hubertciebiada/open-ambient-sensor/hardware/photos/v0.54-mounted-led-ring.jpg

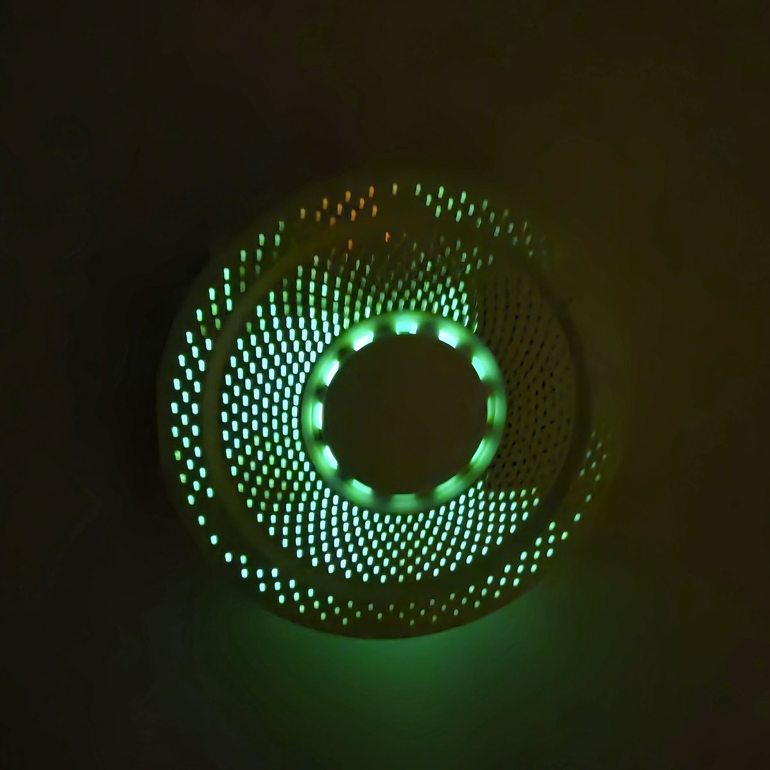
hardware/photos/v0.54-mounted-led-ring.jpg
