hubertciebiada/open-ambient-sensor/hardware/renders/pcb/2d-bottom.png

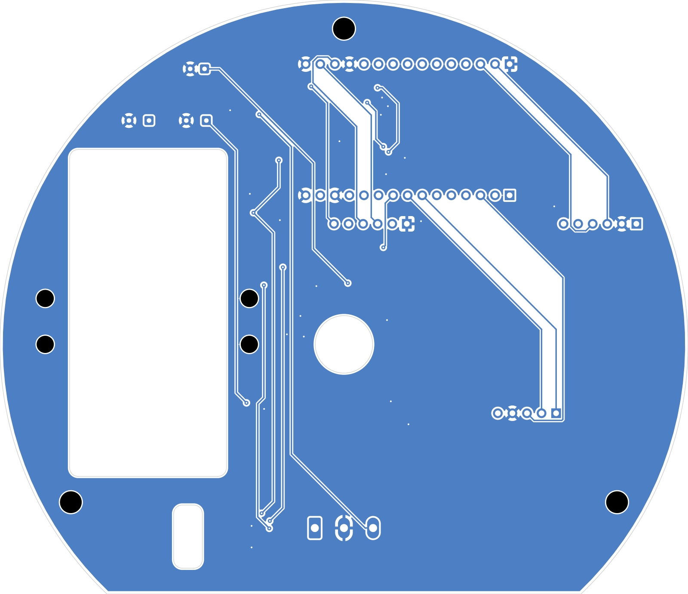
hardware/renders/pcb/2d-bottom.png
