hubertciebiada/open-ambient-sensor/hardware/renders/pcb/2d-cutouts.png

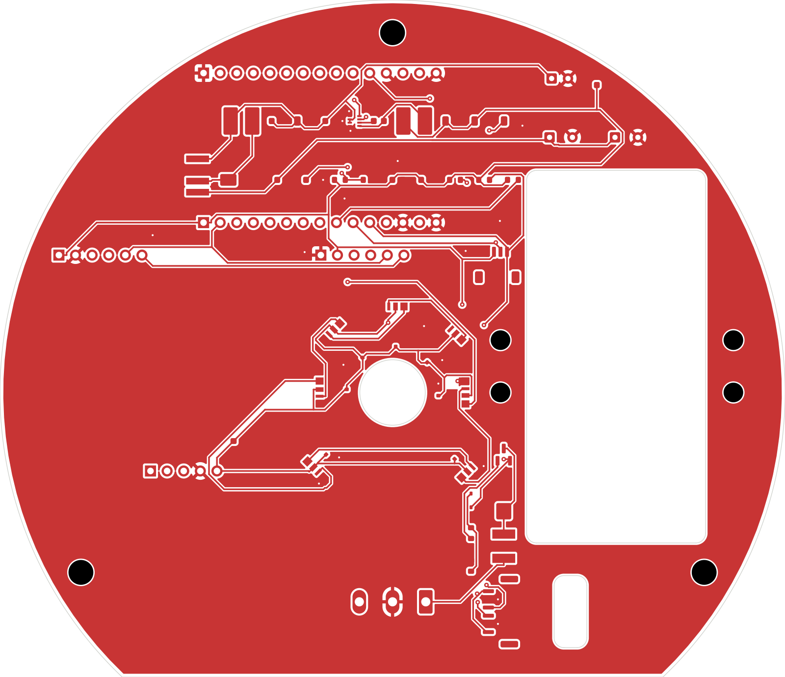
hardware/renders/pcb/2d-cutouts.png
