hubertciebiada/open-ambient-sensor/hardware/renders/pcb/3d-iso-90.png

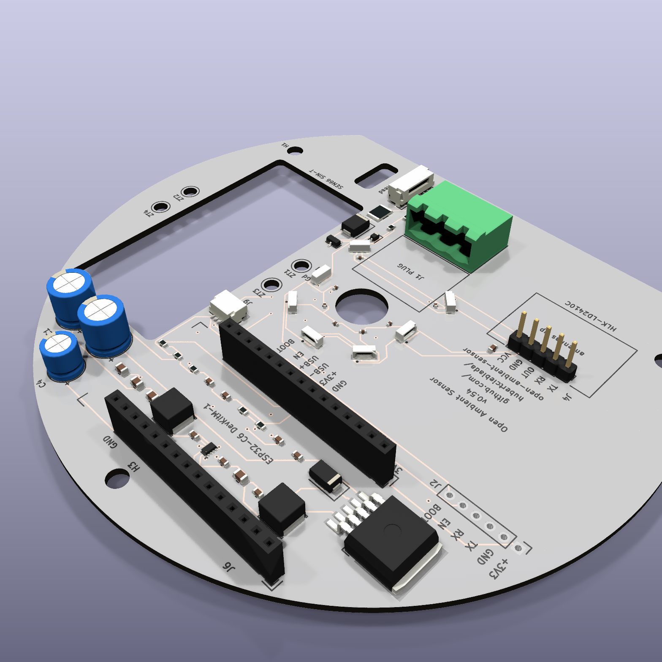
hardware/renders/pcb/3d-iso-90.png
