hubertciebiada/open-ambient-sensor/hardware/renders/pcb/3d-iso-270.png

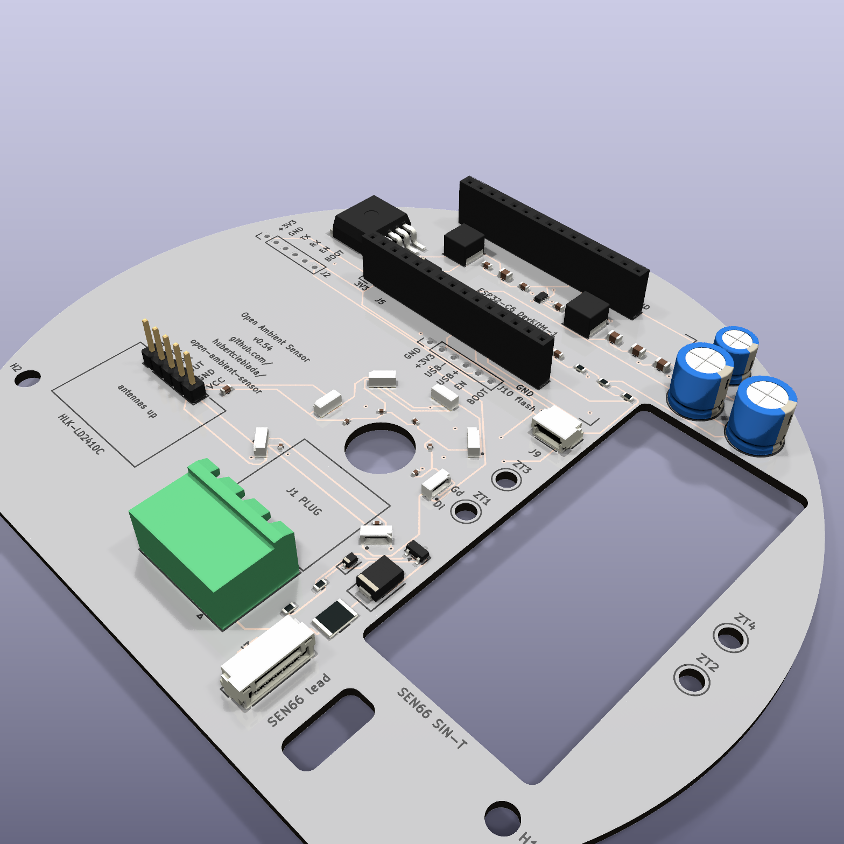
hardware/renders/pcb/3d-iso-270.png
