hubertciebiada/open-ambient-sensor/hardware/renders/sch/sch-io.png

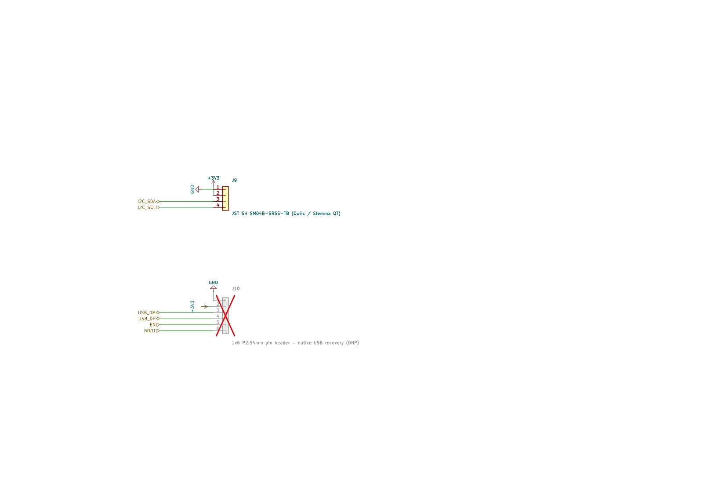
hardware/renders/sch/sch-io.png
