hubertciebiada/open-ambient-sensor/hardware/renders/sch/sch-mcu.png

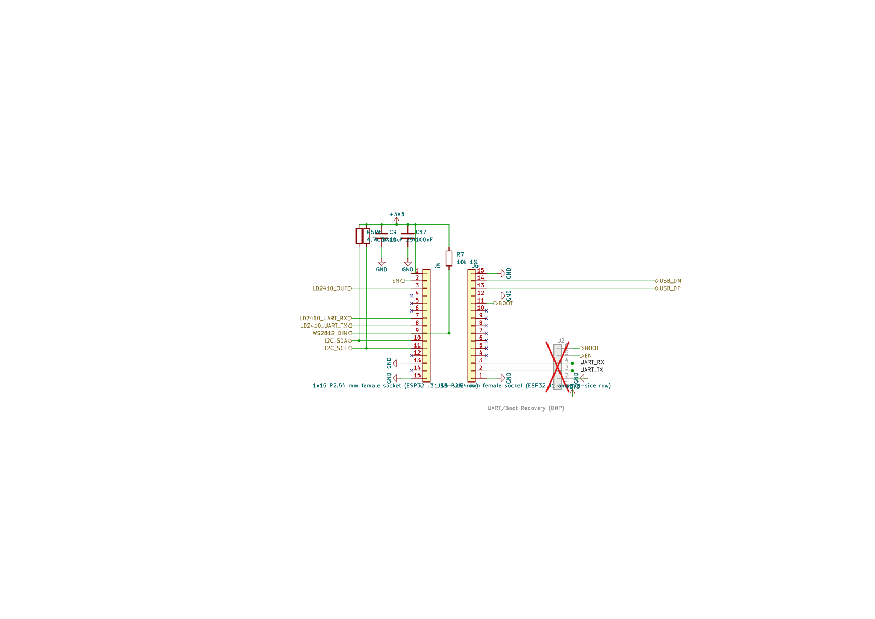
hardware/renders/sch/sch-mcu.png
