hubertciebiada/open-ambient-sensor/hardware/renders/sch/sch-power.png

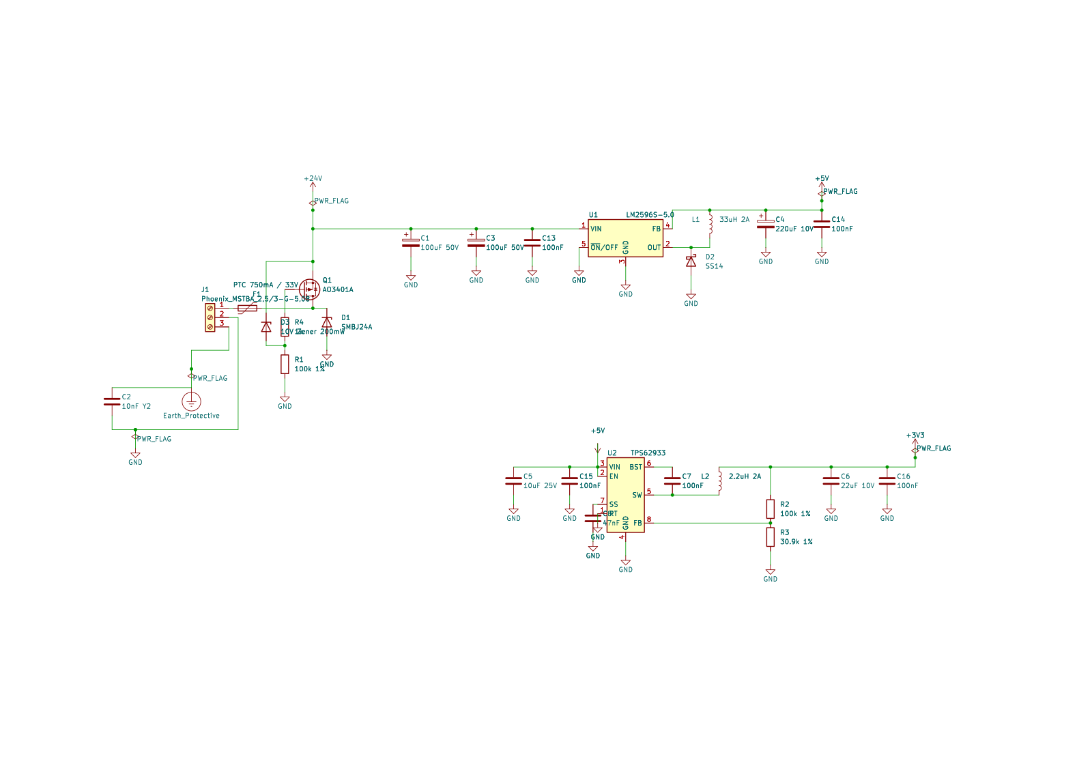
hardware/renders/sch/sch-power.png
