hubertciebiada/open-ambient-sensor/hardware/renders/sch/sch-sensors.png

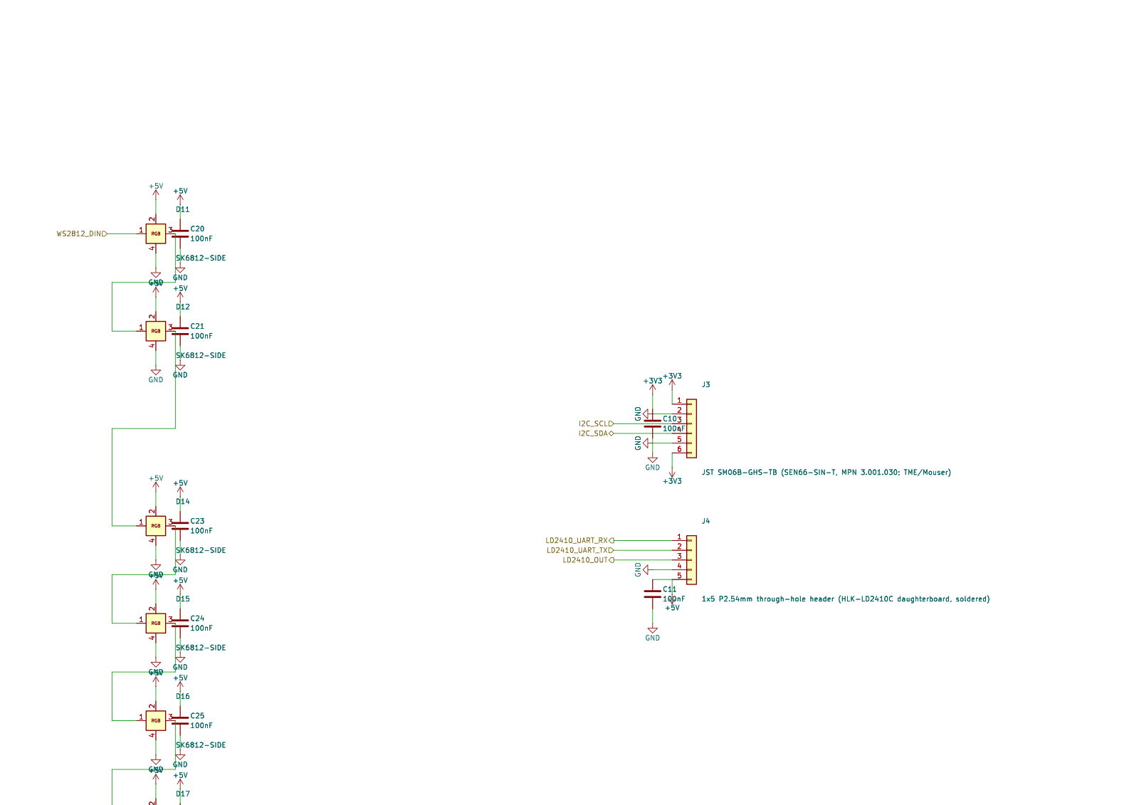
hardware/renders/sch/sch-sensors.png
