hubertciebiada/open-ambient-sensor/hardware/kicad/pipeline/oas/19_check_oas_metadata.py

"""Stage 19: metadata integrity checks on OAS source-of-truth dicts.

Five checks, one stage:

A. `boardgen._project.EXTERNAL_MODULES` (Lesson 10): every dev-module /
   dev-board / breakout entry MUST carry at least one canonical part
   identifier. We accept ANY of:
     - `mpn`                 (manufacturer part number)
     - `ean`                 (EAN/GTIN — Polish/EU retail preferred)
     - `material`            (Sensirion's canonical SKU)
     - `supplier_*` field    (specific distributor SKU or URL)
   Pure descriptive entries ('ESP32-C6 SuperMini' without MPN/EAN) are
   exactly the foot-gun this check prevents.

B. `lcsc_mapping.LCSC_MAPPING` self-consistency (Gap H + Lesson 5):
   - LCSC key matches pattern `^C\\d+$`,
   - `library` ∈ {Basic, Extended, N/A},
   - `manufacturer` and `mpn` both non-empty strings,
   - `datasheet` is a string (URL or empty placeholder).

   These guard against copy-paste typos like `C2302` vs `C23022` where
   one digit off lands on a completely different part (Lesson 5 R3
   near-miss: C23022 = 30.9 kΩ vs C23116 = 806 Ω).

C. `boardgen._project.POWER_BUDGET` schema (Lesson 6 — don't hallucinate
   datasheet values): every entry MUST carry
     - `name`, `rail`, `typ_ma`, `peak_ma`, `datasheet`,
   and the `datasheet` MUST be a non-empty HTTP/HTTPS URL. This forces
   anyone touching the power budget to cite a real datasheet — caught
   the same class of "I remember the AO3401A is ±20 V Vgs" error
   audit-16 caught (actually ±12 V) before it can land in the budget.

D. J4 (HLK-LD2410C) pin order vs Lesson 20 canonical mapping. Authority:
   Hi-Link HLK-LD2410C manual V1.00 (2022-11-07) Table 1 / section 4.2,
   read with the module ANTENNA-FACE UP and its pin row along the north
   edge (board-owner spec, 2026-07-21) — pin 1 = UART Tx, pin 2 = UART
   Rx, pin 3 = OUT, pin 4 = GND, pin 5 = VCC. Two anchors are verified:
     - `boardgen/_sch_sensors.py` J4 wiring block: each J4 pin's wire
       (uuid tags "j4-p1-tx" … "j4-p5-vcc-down") must terminate at the
       canonical net. Net-name nuance: the OAS net names are MCU-centric,
       so J4 pin 1 (the module's UART_Tx OUTPUT) lands on net
       LD2410_UART_RX (it arrives at the ESP32's RX, GPIO 0) and J4 pin 2
       (the module's UART_Rx INPUT) lands on net LD2410_UART_TX (driven
       by GPIO 1) — the standard TX/RX crossover.
     - `boardgen/_project.py::J4_PCB_ROTATION` must stay 90 — the
       rotation that puts pad 1 at the WEST end of the row, where the
       module's Tx pin physically lands under the orientation above.
   This spot is regression-prone twice over: the -B era already burned a
   v0.15.8 schematic reversal that was really a footprint-orientation bug
   (re-fixed at the footprint layer in v0.43), and v0.53 / issue #9 then
   MIRRORED the whole order when the part changed from -B (1 = OUT … 5 =
   VCC) to -C. The check also FAILS LOUDLY if any anchor vanishes (a
   moved/renamed structure means the check is blind, which is itself a
   failure).

E. J3 (SEN66) pin order vs Lesson 21 canonical mapping. Authority:
   Sensirion SEN6x datasheet v0.92 (Dec 2025), Table 16 (p. 15) gives
   the MODULE-side receptacle pinout (1=VDD, 2=GND, 3=SDA, 4=SCL,
   5=GND, 6=VDD). The OAS board-side J3 MUST be the positional MIRROR
   of that table — 1=VDD, 2=GND, **3=SCL, 4=SDA**, 5=GND, 6=VDD —
   because a standard flat parallel-wire JST GH lead reverses pin
   positions between two face-to-face polarized headers (position k
   mates position 7-k end-to-end), and Sensirion's power-symmetric
   pinout (1/6 and 2/5 internally tied) hides the mirror on power so
   it manifests ONLY as an SDA<->SCL swap. Bench-confirmed 2026-06-30
   on the v0.51 prototypes (issue #6): J3 copied Table 16 pin-for-pin
   and the SEN66 never ACKed until firmware swapped the I2C pins.
   Anchored to the "j3-p1-vdd-up" … "j3-p6-vdd-down" wire tags in
   `boardgen/_sch_sensors.py`; fails loudly if anchors vanish. No
   PCB-rotation anchor is needed (unlike J4): the GH socket is keyed,
   so pad-to-cable-position mapping is fixed by the footprint
   regardless of J3_ROTATION.
"""
from __future__ import annotations

import re
import sys
from pathlib import Path

sys.path.insert(0, str(Path(__file__).parent.parent))
from _common import Stage, KICAD_ROOT  # noqa: E402

STAGE_NAME = "check_oas_metadata"

LCSC_PATTERN = re.compile(r"^C\d+$")
LIBRARY_TIERS = {"Basic", "Extended", "N/A"}

# POWER_BUDGET entries must cite a real datasheet URL (Lesson 6 — don't
# hallucinate datasheet values). Empty / placeholder / "TBD" strings are
# rejected. We require the value to START with an http(s):// URL token;
# anything after (e.g. " (search LD2410C)") is descriptive and tolerated
# because some manufacturer datasheet roots have no direct deep-link.
DATASHEET_URL_PATTERN = re.compile(r"^https?://\S+")
POWER_BUDGET_REQUIRED_KEYS = ("name", "rail", "typ_ma", "peak_ma", "datasheet")
POWER_BUDGET_VALID_RAILS = {"3V3", "5V", "24V"}

# At least one of these keys (case-sensitive) must be present in every
# EXTERNAL_MODULES entry. Suffix match counts (so "supplier_pl",
# "supplier_eu", "supplier_global" all satisfy the "supplier_*" intent).
IDENTITY_KEYS = ("mpn", "ean", "material")
IDENTITY_KEY_PREFIXES = ("supplier",)

# --- Check D: J4 / LD2410C pin order (Lesson 20) ------------------------------
# Canonical order per the Hi-Link HLK-LD2410C manual V1.00 (2022-11-07)
# Table 1 / section 4.2, read against the board-owner's orientation spec
# (2026-07-21 — antennas UP, pin row along the module's north edge, pin 1
# at the WEST end): pin 1 = UART Tx, 2 = UART Rx, 3 = OUT, 4 = GND,
# 5 = VCC.
#
# ⚠ This is the MIRROR of the -B order this check enforced before v0.53 /
# issue #9 (1 = OUT, 2 = Tx, 3 = Rx, 4 = GND, 5 = VCC). A future audit
# quoting the -B mapping — or quoting espboards.dev's "VCC, GND, TX, RX,
# OUT", which is the -C row read from the far end — is wrong.
#
# The schematic source of truth is the J4 wiring block in
# boardgen/_sch_sensors.py (no importable pin→net dict exists — the mapping
# lives inside the sheet-generator function body), so we parse the source
# text anchored on the deterministic wire uuid tags. Each entry:
#   pin -> (wire uuid tag, anchor kind, expected net/lib_id).
#
# TX/RX crossover: net names are MCU-centric. J4 pin 1 is the module's
# UART_Tx OUTPUT — it drives the ESP32's RX (GPIO 0), hence net
# LD2410_UART_RX. J4 pin 2 is the module's UART_Rx INPUT — driven by the
# ESP32's TX (GPIO 1), hence net LD2410_UART_TX. (The pair carried the
# bare names UART_TX / UART_RX while it sat on GPIO 16/17; those names now
# belong to the console at J2 — CLAUDE.md Lesson 23.) Pin 5 (VCC) is fed
# from the +5V rail (LM2596S), so its anchor is the power:+5V flag.
SCH_SENSORS_SOURCE_REL = Path("boardgen") / "_sch_sensors.py"
J4_EXPECTED: dict[int, tuple[str, str, str]] = {
    1: ("j4-p1-tx", "label", "LD2410_UART_RX"),  # module TX -> MCU RX (crossover)
    2: ("j4-p2-rx", "label", "LD2410_UART_TX"),  # module RX <- MCU TX (crossover)
    3: ("j4-p3-out", "label", "LD2410_OUT"),
    4: ("j4-p4-gnd-hop", "power", "power:GND"),
    5: ("j4-p5-vcc-down", "power", "power:+5V"),
}
# Net/flag must appear in the parts.append(...) call immediately following
# the anchored wire — 600 chars is comfortably past the intervening
# coordinate arguments but well short of the NEXT pin's wiring.
ANCHOR_WINDOW = 600
HLABEL_PATTERN = re.compile(r'_sch_hierarchical_label\(\s*name="([A-Za-z0-9_]+)"')
PWRFLAG_PATTERN = re.compile(r'_sch_power_flag\(\s*lib_id="([A-Za-z0-9_:+\-]+)"')

# --- Check E: J3 / SEN66 pin order (Lesson 21) --------------------------------
# Canonical J3 (board-side) order = positional MIRROR of Sensirion SEN6x
# datasheet v0.92 Table 16 (p. 15): 1=VDD, 2=GND, 3=SCL, 4=SDA, 5=GND,
# 6=VDD. Table 16 is the MODULE side; a standard flat parallel-wire JST GH
# lead maps position k to position 7-k between the two face-to-face keyed
# headers, and the power-symmetric SEN6x pinout (1/6, 2/5 internally tied)
# reduces the visible effect of that mirror to an SDA<->SCL swap on pins
# 3/4. Bench-confirmed 2026-06-30 (issue #6). Any future audit asserting
# "J3 pin 3 must be SDA because Table 16 says pin 3 = SDA" is WRONG —
# it confuses the module side with the host side (Lesson 21).
J3_EXPECTED: dict[int, tuple[str, str, str]] = {
    1: ("j3-p1-vdd-up", "power", "power:+3V3"),
    2: ("j3-p2-gnd-hop", "power", "power:GND"),
    3: ("j3-p3-scl", "label", "I2C_SCL"),   # mirror of SEN66 pin 4 (SCL)
    4: ("j3-p4-sda", "label", "I2C_SDA"),   # mirror of SEN66 pin 3 (SDA)
    5: ("j3-p5-gnd-hop", "power", "power:GND"),
    6: ("j3-p6-vdd-down", "power", "power:+3V3"),
}
# Rotation 90 puts pad 1 at the WEST end of the row, where the module's Tx
# pin physically lands under the antennas-up orientation (rotation 270 was
# the pre-v0.43 end-for-end-wrong state of the -B era, and the requirement
# survived the -C rework unchanged even though the pin ORDER mirrored). A
# deliberate placement rework must update BOTH J4_PCB_ROTATION and this
# constant.
J4_EXPECTED_PCB_ROTATION = 90


def _has_identity(entry: dict) -> bool:
    if any(k in entry and entry[k] for k in IDENTITY_KEYS):
        return True
    for key in entry:
        for prefix in IDENTITY_KEY_PREFIXES:
            if key.startswith(prefix) and entry[key]:
                return True
    return False


def _check_external_modules(errors: list[str]) -> int:
    sys.path.insert(0, str(KICAD_ROOT))
    from boardgen._project import EXTERNAL_MODULES  # noqa: E402

    for name, entry in EXTERNAL_MODULES.items():
        if not _has_identity(entry):
            present_keys = sorted(entry.keys())
            errors.append(
                f"EXTERNAL_MODULES[{name!r}] missing identifier — needs "
                f"one of {IDENTITY_KEYS} or supplier_* "
                f"(have: {present_keys})"
            )
    return len(EXTERNAL_MODULES)


def _check_lcsc_mapping(errors: list[str]) -> int:
    sys.path.insert(0, str(KICAD_ROOT))
    from lcsc_mapping import LCSC_MAPPING  # noqa: E402

    for key, entry in LCSC_MAPPING.items():
        loc = f"LCSC_MAPPING[{key!r}]"

        lcsc = entry.get("lcsc", "")
        if not LCSC_PATTERN.match(lcsc) and not lcsc.startswith("DEPRECATED-"):
            errors.append(
                f"{loc}['lcsc'] = {lcsc!r} — must match ^C\\d+$"
            )

        lib = entry.get("library", "")
        if lib not in LIBRARY_TIERS:
            errors.append(
                f"{loc}['library'] = {lib!r} — must be one of {sorted(LIBRARY_TIERS)}"
            )

        for field in ("manufacturer", "mpn"):
            v = entry.get(field, "")
            if not v.strip():
                errors.append(f"{loc}[{field!r}] missing or empty")

        # Datasheet field: only required to be present (URL or empty
        # placeholder). Type narrows to `str` from the dict typing
        # contract, no runtime type check needed.
        entry.get("datasheet", "")

    return len(LCSC_MAPPING)


def _check_power_budget(errors: list[str]) -> int:
    sys.path.insert(0, str(KICAD_ROOT))
    from boardgen._project import POWER_BUDGET  # noqa: E402

    for idx, entry in enumerate(POWER_BUDGET):
        # PowerBudgetEntry is a TypedDict (statically enforced by mypy on
        # boardgen/_project.py). Runtime is always a dict here; the legacy
        # `isinstance(entry, dict)` defensive branch was unreachable.
        loc = f"POWER_BUDGET[{idx}]"
        if entry.get("name"):
            loc = f"POWER_BUDGET[{idx}] ({entry['name']!r})"

        for k in POWER_BUDGET_REQUIRED_KEYS:
            if k not in entry:
                errors.append(f"{loc} missing required key {k!r}")

        rail = entry.get("rail", "")
        if rail and rail not in POWER_BUDGET_VALID_RAILS:
            errors.append(
                f"{loc}['rail'] = {rail!r} — must be one of "
                f"{sorted(POWER_BUDGET_VALID_RAILS)}"
            )

        for field in ("typ_ma", "peak_ma"):
            v = entry.get(field)
            if v is None:
                continue  # already reported by required-keys loop
            if not isinstance(v, (int, float)) or isinstance(v, bool):
                errors.append(
                    f"{loc}[{field!r}] = {v!r} — must be int/float (mA)"
                )
            elif v < 0:
                errors.append(
                    f"{loc}[{field!r}] = {v!r} — must be non-negative"
                )

        datasheet = entry.get("datasheet", "")
        if not isinstance(datasheet, str) or not datasheet.strip():
            errors.append(
                f"{loc}['datasheet'] missing or empty — Lesson 6 requires "
                f"a real datasheet URL for every power-budget entry"
            )
        elif not DATASHEET_URL_PATTERN.match(datasheet.strip()):
            errors.append(
                f"{loc}['datasheet'] = {datasheet!r} — must be a real "
                f"http(s):// URL (Lesson 6: don't hallucinate datasheet "
                f"values)"
            )

    return len(POWER_BUDGET)


def _check_connector_pin_anchors(
    errors: list[str],
    conn: str,
    lesson: str,
    expected: dict[int, tuple[str, str, str]],
    canon_msg: str,
) -> int:
    """Shared anchor scanner for checks D (J4) and E (J3).

    For each pin, finds the deterministic wire uuid tag in
    `boardgen/_sch_sensors.py` and asserts the hierarchical label /
    power flag emitted immediately after it matches the canonical net.
    Fails loudly if any anchor vanished: a moved/renamed wiring block
    means the check is blind, which is itself a failure.
    """
    src_path = KICAD_ROOT / SCH_SENSORS_SOURCE_REL
    try:
        src = src_path.read_text(encoding="utf-8")
    except OSError as exc:
        errors.append(
            f"{conn} ({lesson}) check is blind — cannot read "
            f"{src_path}: {exc}"
        )
        return 0

    checked = 0
    for pin, (tag, kind, expected_net) in sorted(expected.items()):
        pos = src.find(f'"{tag}"')
        if pos < 0:
            errors.append(
                f"{conn} pin {pin}: wire anchor {tag!r} not found in "
                f"{SCH_SENSORS_SOURCE_REL} — the {conn} wiring block moved "
                f"or was renamed; the {lesson} check is blind and must be "
                f"re-anchored"
            )
            continue

        window = src[pos:pos + ANCHOR_WINDOW]
        if kind == "label":
            m = HLABEL_PATTERN.search(window)
            what = "hierarchical label"
        else:
            m = PWRFLAG_PATTERN.search(window)
            what = "power flag"
        if m is None:
            errors.append(
                f"{conn} pin {pin}: no {what} found after wire anchor "
                f"{tag!r} in {SCH_SENSORS_SOURCE_REL} — structure changed; "
                f"the {lesson} check is blind and must be re-anchored"
            )
            continue

        actual = m.group(1)
        if actual != expected_net:
            errors.append(
                f"{conn} pin {pin}: {what} {actual!r} != canonical "
                f"{expected_net!r} — {canon_msg}"
            )
            continue
        checked += 1
    return checked


def _check_j4_pin_order(errors: list[str]) -> int:
    """Check D: J4 pin 1..5 net order vs Lesson 20 canonical mapping.

    Authority: Hi-Link HLK-LD2410C manual V1.00 Table 1 / section 4.2 —
    1=UART Tx, 2=UART Rx, 3=OUT, 4=GND, 5=VCC (MCU-centric net names
    UART_RX / UART_TX on pins 1 / 2 — see the J4_EXPECTED comment for
    the TX/RX crossover). Fails loudly if any anchor vanished: a
    moved/renamed J4 wiring block or J4_PCB_* constant means this check
    is blind, which is itself a failure.
    """
    sys.path.insert(0, str(KICAD_ROOT))
    import boardgen._project as _bg_project  # noqa: E402

    checked = _check_connector_pin_anchors(
        errors,
        conn="J4",
        lesson="Lesson-20",
        expected=J4_EXPECTED,
        canon_msg=(
            "Lesson 20 / HLK-LD2410C manual V1.00 Table 1 (section 4.2), "
            "read antennas-up with the pin row north: 1=module TX (net "
            "UART_RX), 2=module RX (net UART_TX), 3=OUT, 4=GND, 5=VCC. "
            "The MIRRORED order 1=OUT..5=VCC belonged to the HLK-LD2410B "
            "and was retired in v0.53 / issue #9"
        ),
    )

    rotation = getattr(_bg_project, "J4_PCB_ROTATION", None)
    if rotation is None:
        errors.append(
            "J4_PCB_ROTATION vanished from boardgen/_project.py — the "
            "Lesson-20 placement anchor is blind and must be re-anchored"
        )
    elif rotation != J4_EXPECTED_PCB_ROTATION:
        errors.append(
            f"J4_PCB_ROTATION = {rotation!r} != {J4_EXPECTED_PCB_ROTATION} "
            f"— rotation 90 puts pad 1 at the WEST end of the row, where "
            f"the LD2410C's TX pin physically lands when the module is "
            f"seated antennas-up (270 was the pre-v0.43 end-for-end wrong "
            f"state). A deliberate placement rework must update both the "
            f"constant and this check (Lesson 20)"
        )
    return checked


def _check_j3_pin_order(errors: list[str]) -> int:
    """Check E: J3 pin 1..6 net order vs Lesson 21 canonical mapping.

    Authority: Sensirion SEN6x datasheet v0.92 (Dec 2025) Table 16
    (p. 15) — the MODULE-side pinout. The board-side J3 must be its
    positional MIRROR (1=VDD, 2=GND, 3=SCL, 4=SDA, 5=GND, 6=VDD)
    because a standard flat parallel-wire JST GH lead reverses pin
    positions between the two face-to-face keyed headers; the
    power-symmetric SEN6x pinout hides the mirror on power pins, so the
    only visible effect is the pins-3/4 SDA<->SCL swap that bricked the
    SEN66 on the v0.51 prototypes (issue #6, bench-confirmed
    2026-06-30). No PCB-rotation anchor (unlike check D): the GH socket
    is keyed, so the pad-to-cable-position mapping is fixed by the
    footprint regardless of J3_ROTATION.
    """
    return _check_connector_pin_anchors(
        errors,
        conn="J3",
        lesson="Lesson-21",
        expected=J3_EXPECTED,
        canon_msg=(
            "Lesson 21 / SEN6x datasheet v0.92 Table 16 (p. 15) MIRRORED "
            "for the board side: 1=VDD, 2=GND, 3=SCL, 4=SDA, 5=GND, 6=VDD "
            "(Table 16 itself is the MODULE side — a straight flat GH lead "
            "mirrors positions end-to-end)"
        ),
    )


def main() -> int:
    with Stage(STAGE_NAME) as st:
        errors: list[str] = []
        n_modules = _check_external_modules(errors)
        n_lcsc = _check_lcsc_mapping(errors)
        n_budget = _check_power_budget(errors)
        n_j4 = _check_j4_pin_order(errors)
        n_j3 = _check_j3_pin_order(errors)

        if errors:
            for e in errors:
                print(f"[FAIL] {e}")
            st.fail(f"{len(errors)} metadata integrity violation(s)")

        st.ok(
            f"{n_modules} EXTERNAL_MODULES entries have valid identifiers; "
            f"{n_lcsc} LCSC_MAPPING entries match expected schema; "
            f"{n_budget} POWER_BUDGET entries have valid datasheet URLs; "
            f"{n_j4}/5 J4 pins match Lesson-20 canonical order "
            f"(1=TX 2=RX 3=OUT 4=GND 5=VCC, HLK-LD2410C manual V1.00 "
            f"Table 1); "
            f"{n_j3}/6 J3 pins match Lesson-21 canonical order "
            f"(1=VDD 2=GND 3=SCL 4=SDA 5=GND 6=VDD — mirror of SEN6x "
            f"v0.92 Table 16)"
        )
    return 0


if __name__ == "__main__":
    sys.exit(main())
