hubertciebiada/open-ambient-sensor/hardware/kicad/boardgen/04_schematic_power.py

"""boardgen stage 04: write power.kicad_sch.

First stage to run after the PCB is written, so it lazily builds the
PCB-ref-to-footprint map and the LCSC metadata map for downstream sheet
backfill. Subsequent schematic stages reuse them via ctx.
"""
from __future__ import annotations

import sys
from pathlib import Path

sys.path.insert(0, str(Path(__file__).parent.parent))
from boardgen._common import HERE, sheet_context
from boardgen._postprocess import (
    _build_pcb_ref_to_footprint, _build_lcsc_metadata_map,
    _apply_schematic_footprints, _apply_schematic_lcsc_metadata,
)
from boardgen._sch_power import gen_power_sch


def _ensure_metadata(ctx) -> None:
    if not ctx.pcb_ref_to_fp:
        ctx.pcb_ref_to_fp = _build_pcb_ref_to_footprint()
    if not ctx.lcsc_metadata_map:
        ctx.lcsc_metadata_map = _build_lcsc_metadata_map()


def run(ctx) -> None:
    _ensure_metadata(ctx)
    with sheet_context("power"):
        content = gen_power_sch()
    content = _apply_schematic_footprints(content, ctx.pcb_ref_to_fp)
    content = _apply_schematic_lcsc_metadata(content, ctx.lcsc_metadata_map)
    (HERE / "power.kicad_sch").write_text(content, encoding="utf-8")


if __name__ == "__main__":
    from boardgen._common import Context
    run(Context())
