hubertciebiada/open-ambient-sensor/hardware/kicad/pipeline/generic/11_render_sch.py

"""Stage 11/11: schematic SVG renders.

kicad-cli sch export svg writes one SVG per schematic file into the
output directory, naming it after the input file's stem (e.g. power.svg).
We render each hierarchical sub-sheet directly (passing its file) so we
get one clean SVG per sub-sheet, then rename to sch-<name>.svg for a
consistent and gitignore-friendly output set.
"""
from __future__ import annotations

import shutil
import sys
from pathlib import Path

sys.path.insert(0, str(Path(__file__).parent.parent))
from _common import Stage, run, find_kicad_cli, RENDERS, KICAD_ROOT  # noqa: E402
from _project import SCH_SUB_SHEETS  # noqa: E402

STAGE_NAME = "render_sch"


def main() -> int:
    with Stage(STAGE_NAME) as st:
        kcli = find_kicad_cli()
        RENDERS.mkdir(exist_ok=True)

        for subdir, out_name, src_name in SCH_SUB_SHEETS:
            out_dir = RENDERS / subdir
            out_dir.mkdir(parents=True, exist_ok=True)
            src = KICAD_ROOT / src_name
            # Render into a temp subdir (prefixed `_` so it stays gitignored
            # along with the DRC/ERC reports), then atomically move the
            # produced file into renders/<subdir>/ under the desired
            # sch-<name>.svg filename. shutil.rmtree() handles the case
            # where kicad-cli on the hierarchical root dumps every sub-sheet
            # into tmp_dir (we keep just the one we asked for).
            tmp_dir = RENDERS / f"_{out_name}-tmp"
            tmp_dir.mkdir(exist_ok=True)
            run([
                kcli, "sch", "export", "svg",
                "--output", str(tmp_dir),
                "--exclude-drawing-sheet",
                "--no-background-color",
                str(src),
            ], hide_output=True)
            produced = tmp_dir / f"{src.stem}.svg"
            final = out_dir / f"{out_name}.svg"
            produced.replace(final)
            shutil.rmtree(tmp_dir, ignore_errors=True)
            st.ok(f"wrote {subdir}/{final.name}")
    return 0


if __name__ == "__main__":
    sys.exit(main())
