hubertciebiada/open-ambient-sensor/hardware/kicad/pipeline/generic/13_render_3d.py

"""Stage 13/11: 3D PCB renders (expensive — ~15 s each).

Renders two views via `kicad-cli pcb render`:
  - 3d-top.png   straight-down top view
  - 3d-iso.png   isometric (--rotate '-45,0,45' --perspective --floor)
"""
from __future__ import annotations

import sys
from pathlib import Path

sys.path.insert(0, str(Path(__file__).parent.parent))
from _common import Stage, run, find_kicad_cli, RENDERS  # noqa: E402
from _project import PCB_PATH, PCB_3D_TARGETS  # noqa: E402

STAGE_NAME = "render_3d"


def main() -> int:
    with Stage(STAGE_NAME) as st:
        kcli = find_kicad_cli()
        RENDERS.mkdir(exist_ok=True)

        for subdir, out_name, extra in PCB_3D_TARGETS:
            out_dir = RENDERS / subdir
            out_dir.mkdir(parents=True, exist_ok=True)
            st.info(f"rendering {subdir}/{out_name} (~15s)")
            run([
                kcli, "pcb", "render",
                "--output", str(out_dir / out_name),
                "--side", "top",
                "--width", "1600", "--height", "1600",
                "--background", "opaque",
                "--quality", "high",
                *extra,
                str(PCB_PATH),
            ], hide_output=True)
            st.ok(f"wrote {subdir}/{out_name}")
    return 0


if __name__ == "__main__":
    sys.exit(main())
