hubertciebiada/open-ambient-sensor/hardware/kicad/boardgen/_project.py

"""boardgen/_project.py — OAS-specific constants and geometry.

This module holds everything that DEFINES the OAS board as a specific
electronic product:

  - Project identity (PROJECT_NAME, PROJECT_SHORTNAME)
  - External-module metadata (EXTERNAL_MODULES — Espressif devkit, SEN66,
    LD2410, AK-N-94 enclosure)
  - ESP32-C6 GPIO pin assignments (GPIO_ASSIGNMENTS, GPIO_RESERVED,
    GPIO_SPARE — single source of truth for the pinout)
  - PCB geometry (Ø120 mm D-shape outline, mounting holes, cable hole,
    case-wall cutouts)
  - Daughterboard placements: SEN66 + zip-tie holes + J3 socket;
    LD2410 + J4 socket; ESP32-C6 DevKitM-1;
    J1 24 V terminal block; J9 Qwiic; J10 recovery header
  - AQI LED ring (8 × SK6812-SIDE on 45° pitch)
  - Local-to-PCB coordinate transforms (`_sen66_local_to_pcb`,
    `_ld2410_local_to_pcb`, `_led_local_to_pcb`)
  - Page-centring formatters fx/fy

Project-AGNOSTIC framework helpers (UUID system, `fmt`, `Context`,
sub-sheet IDs, KiCad format versions) live in `boardgen/_common.py`.
"""
from __future__ import annotations

import math
from typing import NotRequired, TypedDict

from boardgen._common import fmt


class PowerBudgetEntry(TypedDict):
    name: str
    rail: str
    typ_ma: float
    peak_ma: float
    datasheet: str
    note: NotRequired[str]
    radio_group: NotRequired[str]

# =============================================================================
# PROJECT METADATA
# =============================================================================
# Single source of truth for project identity, external modules, and GPIO
# map. Consumed by:
#   - boardgen stages themselves (title block / silk text; legacy
#     constants like OAS_VERSION_LINE still drive existing renders today)
#   - pipeline/oas/06_check_boot.py (could cross-check GPIO_ASSIGNMENTS)
#   - downstream documentation (CLAUDE.md references constants by name)
#
# Update HERE FIRST when changing identity / pinout / external modules.
# Other places (CLAUDE.md quick-reference tables, schematic generators)
# follow this dict.

# Project identity --------------------------------------------------------
PROJECT_NAME = "Open Ambient Sensor"
PROJECT_SHORTNAME = "OAS"

# External modules (manual-source / 3rd-party — NOT in lcsc-mapping.csv
# because they go through THT hand-solder, separate procurement, or are
# mechanical). Each entry: full identification metadata for re-procurement.
EXTERNAL_MODULES = {
    "ESP32-C6-DevKitM-1-N4": {
        "manufacturer": "Espressif",
        "mpn": "ESP32-C6-DevKitM-1-N4",
        "ean": "5904422385651",
        "supplier_pl": "Botland",
        "datasheet": (
            "https://docs.espressif.com/projects/esp-dev-kits/en/latest/"
            "esp32c6/esp32-c6-devkitm-1/index.html"
        ),
        "note": (
            "Official Espressif devkit (ESP32-C6-MINI-1 SoM + 2x USB-C). "
            "NOT compatible with generic 'SuperMini' clones (different pinout)."
        ),
        "derived_dimensions": (
            "PCB body 48.26 x 25.4 mm; the ESP32-C6-MINI-1 PCB antenna adds a "
            "13.20 x 5.37 mm tab overhanging one short edge -> total envelope "
            "~53.6 x 25.4 mm. Body 48.26 / 25.4 / pin geometry AND the "
            "antenna tab (width 13.20, protrusion 5.37) all from the Espressif "
            "dimensions PDF. Mounts 8.6 mm above the OAS PCB on 2x 1x15 P2.54 "
            "female sockets (J5/J6)."
        ),
    },
    "SEN66-SIN-T": {
        "manufacturer": "Sensirion",
        "material": "3.001.030",
        "supplier_global": "Sensirion direct",
        "supplier_eu": "LaskaKit / ThePiHut",
        "datasheet": "https://sensirion.com/resource/datasheet/SEN66",
        "accessory": (
            "JST GH 6-pin cable (50 cm AWG26) - separately ordered; "
            "Sensirion ships SEN66 without cable. MUST be the flat "
            "parallel-wire style (both housings crimped on the same face "
            "of the wire row) - an opposite-crimp, position-1:1 lead "
            "(Qwiic-cable style) re-crosses SDA/SCL on the corrected J3 "
            "(CLAUDE.md Lesson 21, issue #6)."
        ),
        "note": (
            "Combo sensor: NDIR CO2 + laser PM + MOX VOC/NOx + SHT (T/RH) "
            "in single ~25 x 55 x 21.5 mm module."
        ),
    },
    "HLK-LD2410C": {
        "manufacturer": "Hi-Link",
        "mpn": "HLK-LD2410C",
        "supplier": "HiLink direct / reputable distributor",
        "supplier_note": (
            "Buy from a reputable distributor, NOT the cheapest "
            "marketplace listing (GitHub issue #9: two LD2410B units from "
            "different sellers, both on firmware build 2.44.25070917, "
            "shipped with a permanently mute UART TX). LCSC lists a "
            "HLK-LD2410C-P variant (C19723500) whose -P suffix is not "
            "documented by Hi-Link — confirm what it denotes before "
            "ordering that SKU."
        ),
        "datasheet": "https://www.hlktech.net/index.php?id=1095",
        "note": (
            "Specifically the -C variant (v0.53, GitHub issue #9). The "
            "-B variant it replaces is a 35 x 7 mm strip with a 1.27 mm "
            "castellated pad row and pin order OUT/Tx/Rx/GND/VCC; the -C "
            "is a 22 x 16 mm board with a 2.54 mm through-hole row and "
            "pin order Tx/Rx/OUT/GND/VCC — same radar, same 256000-baud "
            "protocol, NOT footprint- or pin-compatible. Pinout per "
            "HLK-LD2410C manual V1.00 (2022-11-07) Table 1, section 4.2; "
            "pin 1 (Tx) carries the square pad, pins 2..5 are round. "
            "See CLAUDE.md Lesson 20."
        ),
        "derived_dimensions": (
            "PCB body 22.0 x 16.0 mm (manual V1.00 section 4.1 + Table "
            "2). 5 plated holes, 2.54 mm pitch, hole Ø0.9 mm, on the "
            "22 mm long edge, row centred (pin 1 at 5.92 mm = "
            "(22 - 4x2.54)/2 from the adjacent short edge). Pin-row "
            "inset from the pinned long edge ~1.42 mm and the two "
            "antenna patches (each ~3.95 x 5.42 mm, spanning 4.50..9.92 "
            "mm from that edge, at 3.28..7.23 and 14.83..18.78 mm from "
            "the short edge) are MEASURED off the to-scale Figure 5 of "
            "the manual, not dimensioned by Hi-Link — RE-VERIFY WITH "
            "CALIPERS ON THE DELIVERED MODULE BEFORE THE NEXT PCB ORDER "
            "(issue #9 acceptance criterion). Module thickness is not "
            "stated anywhere by Hi-Link; components sit on BOTH faces "
            "(radar QFN + patches on the antenna face, LDO + 2 crystals "
            "on the back), so the standoff budget also needs a caliper "
            "check."
        ),
    },
    "SZOMK AK-N-94": {
        "manufacturer": "SZOMK",
        "mpn": "AK-N-94",
        "description": (
            "Ø128 mm perforated white ABS enclosure "
            "(smoke-detector form factor)"
        ),
        "supplier": "SZOMK direct (chinaenclosure.com)",
        "datasheet_note": (
            "Manufacturer DXF / datasheet are 3rd-party and NOT "
            "redistributable via this repo (CLAUDE.md Rule 6). Keep "
            "locally; gitignored."
        ),
        "derived_dimensions": (
            "PCB Ø120 D-shape, 3x M3 mounting (Ø3.8 NPTH) on Ø110 pitch, "
            "Ø10 central cable pass-through, 17 mm front clearance / "
            "22 mm in SEN66 zone, 5 mm back."
        ),
    },
}

# ESP32-C6-DevKitM-1-N4 GPIO assignments (single source of truth for pinout).
# Each entry: {net: <name>, desc: <description>}. Update HERE first when
# re-pinning, then the schematic generators below pick up via the table.
# Cross-checked by pipeline/oas/06_check_boot.py.
GPIO_ASSIGNMENTS = {
    0:  {"net": "LD2410_UART_RX", "sheet": "/MCU/", "desc": "UART1 RX <- LD2410C Tx (J4 pin 1) at 256000 baud. J5 pin 7"},
    1:  {"net": "LD2410_UART_TX", "sheet": "/MCU/", "desc": "UART1 TX -> LD2410C Rx (J4 pin 2) at 256000 baud. J5 pin 8"},
    2:  {"net": "LD2410_OUT", "sheet": "/MCU/", "desc": "LD2410 presence interrupt (safe non-strap input)"},
    6:  {"net": "I2C_SDA",    "sheet": "/IO/",  "desc": "Shared I2C bus: SEN66 0x6B, J9 Qwiic"},
    7:  {"net": "I2C_SCL",    "sheet": "/IO/",  "desc": "Shared I2C bus, 4.7 kOhm pull-ups on MCU side (220 mm bus)"},
    8:  {"net": "WS2812_DIN", "sheet": "/MCU/", "desc": "SK6812-SIDE AQI ring data line. STRAP PIN - R7 10 kOhm pull-up to +3V3 required (DevKitM-1 onboard pull-up runs off VCC_5V which is unpowered in OAS)"},
    12: {"net": "USB_DM",     "sheet": "/IO/",  "desc": "Native USB-Serial-JTAG D-"},
    13: {"net": "USB_DP",     "sheet": "/IO/",  "desc": "Native USB-Serial-JTAG D+"},
}
# GPIO 0 / GPIO 1 footnote (why they are safe despite their alternate
# function names): on the ESP32-C6 they double as XTAL_32K_P / XTAL_32K_N,
# and the DevKitM-1 carries the whole 32.768 kHz oscillator network — but
# every part of it is DNP on the Espressif schematic (Y1 "32.768KHz(NC)",
# load caps C4/C5 "12pF/50V(5%)(NC)", feedback R1 "10M/0402(NC)"). What IS
# populated is R3 / R2, 0 R 1% links tying module IO0 / IO1 straight to
# header J1 pins 7 / 8. So the pads are electrically bare: no driver, no
# load beyond a few pF of unpopulated footprint. Neither pin is a strap
# pin on the C6 (straps are 4, 5, 8, 9, 15). Read off
# esp32-c6-devkitm-1-schematics.pdf page 2, 2026-07-22.

GPIO_RESERVED = {
    4:  "MTMS (JTAG mode) - strap pin, avoid for general I/O",
    5:  "MTDI (VDD_SPI voltage select) - strap pin, avoid for general I/O",
    9:  "BOOT button on DevKitM-1 - strap pin (NC or /IO/BOOT recovery only)",
    10: "NOT BONDED on ESP32-C6FH4 (internal SiP flash uses this pad)",
    11: "NOT BONDED on ESP32-C6FH4 (internal SiP flash uses this pad)",
    15: "Boot-mode select / JTAG signal source select - strap pin",
    # 16/17 are NOT merely 'the default UART0 pins' — on the DevKitM-1 they
    # are physically shared with a SECOND, ALWAYS-POWERED transceiver, so no
    # peripheral may ever be assigned here again (CLAUDE.md Lesson 23).
    16: (
        "U0TXD console. On the DevKitM-1 it runs through populated 0 R link "
        "R9 to the CP2102N RXD pin 25 (U3 on Espressif's schematic - not to "
        "be confused with the OAS symbol of that name, retired in v0.21). "
        "The bridge's VDD (6) + REGIN (7) "
        "are tied to VCC_3V3 - the BOARD 3.3 V rail OAS drives at J5.1 - so "
        "the bridge is alive with no USB cable attached. Board-side use is "
        "limited to the J2 recovery header (DNP)"
    ),
    17: (
        "U0RXD console. Same 0 R link path (R7) to the CP2102N TXD pin 26, "
        "which is a push-pull OUTPUT and was observed driving HIGH whenever "
        "the BRIDGE is powered (i.e. whenever the unit is) - bench-probed on "
        "a v0.51 board 2026-07-22 with the LD2410 "
        "unpowered and the bridge's own USB port EMPTY: GPIO17 read DRIVEN "
        "(held HIGH against its internal pull-down) while GPIO2/GPIO16 read "
        "FLOATING. Any peripheral output here fights the bridge; this is the "
        "defect that moved the LD2410 UART to GPIO 0/1"
    ),
}

# Safe-non-strap spare GPIOs for future expansion.
# GPIO 3 (J5 pin 4) joined this list when the NFC tag was removed (GitHub
# issue #7) — the former NT3H1101 FD interrupt line is now an unused
# no-connect. GPIO 1 (J5 pin 8) joined it in v0.53 when SW1 was removed
# (GitHub issue #5) and LEFT it again together with GPIO 0 (J5 pin 7) when
# the LD2410C UART moved off GPIO 16/17 onto that adjacent pin pair.
# NOTE: 16 / 17 are NOT spares — see GPIO_RESERVED above.
GPIO_SPARE = [3, 14, 18, 19, 20, 21, 22, 23]

# =============================================================================
# (geometry / footprints / schematic generators follow)
# =============================================================================

# -----------------------------------------------------------------------------
# Geometry (mm)
# -----------------------------------------------------------------------------
# Page setup: A4 = 297 x 210 mm. Origin (0,0) in KiCad page space is the
# top-left corner of the sheet, so we centre the PCB on the page. The
# aux_axis_origin and grid_origin are also set to the PCB centre so the
# user-facing coordinate display in pcbnew still reads (0, 0) at the
# geometric centre of the board.
PAGE_CENTRE_X = 148.5              # A4 width / 2
PAGE_CENTRE_Y = 105.0              # A4 height / 2

R_OUTLINE = 60.0                   # PCB outline radius
CHORD = 82.6545                    # flat chord length (from DXF line measurement)
HALF_CHORD = CHORD / 2.0
Y_CHORD = math.sqrt(R_OUTLINE**2 - HALF_CHORD**2)  # ≈ 43.5237 mm
# Pitch circle for mounting holes
R_PITCH = 55.0
# Three mounting holes: at angles 30°, 150°, 270° in DXF math coords.
# In KiCad screen coords (Y inverted relative to math) we just use the DXF
# delta-from-centroid values directly: +Y = visually down = bottom of board.
HOLE_OFFSET_X = R_PITCH * math.cos(math.radians(30.0))   # 47.631
HOLE_OFFSET_Y = R_PITCH * math.sin(math.radians(30.0))   # 27.500
HOLE_POSITIONS = [
    ( HOLE_OFFSET_X,  HOLE_OFFSET_Y),   # bottom-right of board (near chord)
    (-HOLE_OFFSET_X,  HOLE_OFFSET_Y),   # bottom-left of board (near chord)
    ( 0.0,           -R_PITCH),         # top of board (opposite chord)
]
EDGE_CUTS_WIDTH = 0.1
HOLE_DIAMETER = 3.8                # Ø3.8 mm per manufacturer DXF
# Mounting holes are NPTH (non-plated). The screws go into plastic bosses in
# the AK-N-94 enclosure — no metal chassis to bond to, so a copper pad here
# would just be floating copper.
COURTYARD_RADIUS = HOLE_DIAMETER * 0.75   # ~1.5× hole diameter

# -----------------------------------------------------------------------------
# PCB layout — soft functional grouping (NOT enforced geometrically)
# -----------------------------------------------------------------------------
# As a starting heuristic, the PCB roughly resembles a clock face with power
# on the upper-left, MCU on the upper-right and sensors filling the bottom
# half — 24 V enters through the central cable hole and power flows roughly
# clockwise. This is a hint to keep rails short, not a hard constraint:
# components may cross any imagined boundary if the layout needs it (the
# SEN66 in particular is large and may span what would otherwise be the
# "sensors" region). No separator lines or sector labels are drawn on the
# PCB — the hierarchical schematic sub-sheets (power / mcu / sensors / io)
# are a functional grouping, not a geographic mapping.

# Cable pass-through hole in the centre of the PCB.
# 24 V (and optional PE) wires enter the case from the rear (electrical box
# behind the unit) and pass through this hole to a terminal block mounted on
# the front side of the PCB. Keeping the entry inside the PCB outline
# physically shields the bare wires — they are inaccessible from outside the
# enclosure, even though 24 V DC is nominally SELV.
# Sized for a 3× 1.5 mm² supply cable (e.g. YDY 3×1.5, outer Ø ≈ 8-9 mm).
# v0.50: reduced Ø12 → Ø10 — the cable still passes, and the smaller hole
# lifts the board-edge clearance of the LED-ring decoupling caps clear of
# JLCDFM's "Component to board edge distance" check (0.75 mm W at Ø12 —
# C20/C24/C25/C26/C27 sit at cap radius 7.0 mm; Ø10 gives ~1.7 mm).
CABLE_HOLE_DIAMETER = 10.0

# -----------------------------------------------------------------------------
# Connector cutouts in the enclosure wall along the flat chord
# -----------------------------------------------------------------------------
# The SZOMK AK-N-94 has 5 rectangular openings in the case wall along the
# flat chord. The manufacturer DXF is a bottom-of-enclosure view, so its X
# axis is mirror-flipped relative to the PCB's top-view coordinate frame.
# The C2 RJ45 / Ethernet opening X range below has been mirror-corrected
# about X=0: it now sits on the +X (right) side, X +1.1..+16.8 / 15.7 mm
# wide, hosting J9. Order along the chord, top-of-enclosure view left to
# right: single round hole | two round holes | USB-C | RJ45 Ethernet |
# square (microSD).
#
# Only openings that host a real OAS connector are emitted as keepout
# zones. The others stay physical in the enclosure, but the PCB ends below
# the case wall so an empty keepout would only sterilise routing space.
#
# Tuple: (name, x_min, x_max, y_min, y_max, allow_pads). PCB-local mm,
# +Y toward the chord. y_max = Y_CHORD means the opening runs past the
# chord and the keepout is clipped to the PCB edge. allow_pads=True drops
# `(pads not_allowed)` so a connector's solder pads may live inside the
# opening area (connector body + accessible pads sit in the case-wall
# opening).
#
# The list is currently EMPTY — no case-wall opening hosts an OAS
# connector anymore:
#   - C2 (RJ45 / Ethernet) dropped in the v0.50 rework: it only ever
#     hosted J9 (Qwiic), now relocated INTERNAL (see J9_PCB_* above),
#     and the exported keepout trapped the J1 protection cluster's pads
#     in Freerouting.
#   - USBC (USB-C opening, X -13..-2, ~11 mm) dropped in v0.53 with the
#     SW1 push-button removal (GitHub issue #5): with no component in
#     the opening, its Dwgs.User reservation marker was documentation
#     noise on the drawings.
# The openings remain physical features of the AK-N-94 wall; re-add an
# entry here only when a connector actually moves into one.
CUTOUTS: list[tuple[str, float, float, float, float, bool]] = []


# Page-centre formatters --------------------------------------------------
def fx(x: float) -> str:
    """Format X with PCB-centre-to-page-centre offset."""
    return fmt(x + PAGE_CENTRE_X)


def fy(y: float) -> str:
    """Format Y with PCB-centre-to-page-centre offset."""
    return fmt(y + PAGE_CENTRE_Y)


# -----------------------------------------------------------------------------
# SEN66 PCB placement (mechanical reference + zip-tie holes + J3 socket)
# -----------------------------------------------------------------------------
# v0.6: SEN66 mounts DIRECTLY ON THE PCB (face-up, body 21.3 mm above
# PCB, openings facing UP through the AK-N-94 perforated cover).
# Hard constraint #1 has a SEN66-zone exception (≥22 mm) for this. The
# PCB carries:
#   1. A no-pad mechanical-reference footprint (`SEN66_Mechanical_Reference`)
#      drawn on F.Fab / F.SilkS — marks where the SEN66 body sits and
#      delineates the openings + sealing-divider hint so neighbouring
#      components (LD2410) stay clear.
#   2. Four NPTH zip-tie holes (Ø 3.0 mm) that pinch the SEN66 flat
#      against the PCB. Cut the zip-ties to remove or replace the module.
#   3. The PCB-side JST GH 6-pin socket (J3) that mates with the SEN66's
#      JST GH cable (50 cm reference cable per Sensirion, separate
#      accessory).
#
# Placement (PCB-local mm, origin = PCB centroid; +Y = down on screen =
# toward the chord):
#
#   SEN66 reference: anchor at (SEN66_ANCHOR_X, SEN66_ANCHOR_Y),
#   rotation SEN66_ROTATION. Long axis runs RADIALLY (6:00 direction)
#   so cable runs are short; connector edge points toward
#   PCB center (cable hole) so the JST GH cable has the shortest run.
#
# Rotation 90° in KiCad's convention maps footprint-local +X (long
# axis, connector edge direction) to PCB -Y (upward, toward 12:00 /
# PCB center) and footprint-local +Y (short axis) to PCB +X (rightward,
# toward 3:00). Anchor (0, 0) in footprint coords is the corner of the
# 55.2 × 25.6 mm body face; placing this anchor at PCB (cx, cy) puts
# the body in PCB X = cx..cx+25.6, Y = cy-55.2..cy.
SEN66_ANCHOR_X = 21.5   # v0.53: shifted 2 mm WEST (was 23.5) for the SEN66
                        # recess cutout (issue #2). At the old X=23.5 the body
                        # NE corner (49.1, -33.2) sat only 0.88 mm from the R60
                        # arc, so the +0.75 mm east cutout margin would have
                        # BREACHED the outline. The 2 mm west shift moves the
                        # body east edge to X=47.1 → cutout east edge X=47.85
                        # → NE cutout corner r=58.67 → 1.33 mm rim to the R60
                        # outline (see SEN66_CUTOUT_* below). The protection
                        # cluster tracks this move 3 mm west in
                        # _footprints_placement.py.
SEN66_ANCHOR_Y = 22.0   # v0.9: lifted up 3 mm (was 25). Body bottom Y=22 clears
                        # H1 courtyard top (Y=24.65) by 2.65 mm so the body
                        # right edge is free to enter H1's X range without
                        # courtyard collision. Also opens 3 mm of room
                        # between SEN66 body bottom and J3 north edge.
SEN66_ROTATION = 90   # degrees; long axis radial, connector toward PCB center


def _sen66_local_to_pcb(lx: float, ly: float) -> tuple[float, float]:
    """Transform a footprint-local SEN66 coordinate to PCB-local mm.

    Applies rotation `SEN66_ROTATION` around the footprint anchor, then
    translates so the anchor lands at (SEN66_ANCHOR_X, SEN66_ANCHOR_Y).
    Used to compute the global PCB coordinates of the 4 zip-tie holes
    given their SEN66-local positions.
    """
    a = math.radians(SEN66_ROTATION)
    # Standard 2D rotation, but KiCad +Y is screen-down, so we apply the
    # same matrix as KiCad does internally for footprint rotation.
    cos_a, sin_a = math.cos(a), math.sin(a)
    rx =  cos_a * lx + sin_a * ly
    ry = -sin_a * lx + cos_a * ly
    return (SEN66_ANCHOR_X + rx, SEN66_ANCHOR_Y + ry)


# -----------------------------------------------------------------------------
# SEN66 recess cutout (v0.53, GitHub issue #2)
# -----------------------------------------------------------------------------
# The SEN66 body stands ~21.5 mm above the PCB; on the flat-mount design the
# assembly was too tall for the AK-N-94 lid to close. Fix: cut a REAL
# rectangular opening in the PCB under the module so it RECESSES into the
# enclosure rear space. Bench finding: cutting exactly at the body outline is
# 1-2 mm too tight to press the module in, so the opening is WIDER than the
# body on every side (asymmetric margins — see below).
#
# Body dimensions duplicated here (physical Sensirion SEN6x constant; the real
# source is SEN66_BODY_X / SEN66_BODY_Y in _footprints_custom.py, which imports
# FROM this module — so we cannot import them back without a cycle). The
# cutout is DERIVED from the anchor + rotation via _sen66_local_to_pcb() on the
# four body corners, so any future SEN66_ANCHOR_* / SEN66_ROTATION move drags
# the cutout with it automatically. tests/test_project_constants.py asserts
# these body dims stay in sync with _footprints_custom.py.
_SEN66_BODY_LONG = 55.2    # footprint-local +X extent (== SEN66_BODY_X)
_SEN66_BODY_SHORT = 25.6   # footprint-local +Y extent (== SEN66_BODY_Y)

# Cutout margins are named by PCB direction (not by footprint axis) so they
# stay meaningful under any rotation. East is held smallest: at the body NE
# corner the R60 arc passes only ~0.88 mm away, so a symmetric +1 mm widening
# would breach the outline. The 2 mm west shift of SEN66_ANCHOR_X (v0.53) plus
# east margin held to 0.75 mm keeps the NE cutout corner 1.33 mm inside the
# R60 outline (verified below + by
# tests/test_project_constants.py::test_sen66_cutout_ne_corner_inside_outline).
# West restored 0.8 → 1.0 mm in v0.53 (issue #3). The 0.8 mm trim had been a
# Task-1 compromise: the ESP32 (MOD1) daughterboard-shadow silk east edge sat
# at X=20.30, only 0.20 mm from a 1.0 mm-margin cutout west edge (20.5) →
# silk_edge_clearance. Issue #3 moves the DevKit west (net 6.5 mm); its body
# east edge is now +17.795 (silk corner ticks ~2.7 mm from the cutout, no
# silk_edge issue), so the compromise is obsolete and the full 1.0 mm
# press-fit margin is restored (cutout west edge back to 20.5, short-axis
# slack 1.75 mm total). Cluster D1 east courtyard (≈+19.25) still clears the
# cutout west edge (20.5) by 1.25 mm (≥1.0).
SEN66_CUTOUT_MARGIN_W = 1.0    # PCB -X (west): press-fit clearance
SEN66_CUTOUT_MARGIN_E = 0.75   # PCB +X (east): held small to protect the R60 rim
SEN66_CUTOUT_MARGIN_N = 0.75   # PCB -Y (north): held small (radial caps sit above)
SEN66_CUTOUT_MARGIN_S = 1.0    # PCB +Y (south): press-fit clearance
SEN66_CUTOUT_CORNER_R = 1.5    # rounded corners; ≥1.0 mm for a Ø2 internal mill

_sen66_body_corners_pcb = [
    _sen66_local_to_pcb(0.0, 0.0),
    _sen66_local_to_pcb(_SEN66_BODY_LONG, 0.0),
    _sen66_local_to_pcb(_SEN66_BODY_LONG, _SEN66_BODY_SHORT),
    _sen66_local_to_pcb(0.0, _SEN66_BODY_SHORT),
]
SEN66_CUTOUT_X_MIN = min(c[0] for c in _sen66_body_corners_pcb) - SEN66_CUTOUT_MARGIN_W
SEN66_CUTOUT_X_MAX = max(c[0] for c in _sen66_body_corners_pcb) + SEN66_CUTOUT_MARGIN_E
SEN66_CUTOUT_Y_MIN = min(c[1] for c in _sen66_body_corners_pcb) - SEN66_CUTOUT_MARGIN_N
SEN66_CUTOUT_Y_MAX = max(c[1] for c in _sen66_body_corners_pcb) + SEN66_CUTOUT_MARGIN_S
# With the v0.53 anchor (21.5, 22.0) + rotation 90 this evaluates to
# X 20.50..47.85, Y -33.95..23.0 (a 27.35 x 56.95 mm opening; slack
# 1.75 mm on both axes over the 25.6 x 55.2 mm body).


# Zip-tie hole positions in SEN66-local mm (relative to the body corner
# at (0, 0)). v0.7: both pinch-points now inside the "safe corridor"
# X ∈ [19.22, 31.03] (between inlet-zone X≤18.22 and outlet X≥32.03), so
# a 2 mm zip-tie band centred at each X passes over the body without
# covering any inlet or outlet on the air-side face.
# X = 22 (~40% of 55.2) and X = 30 (~54% of 55.2). Previously the second
# pair was at X=50 which sits inside the outlet circle (X=32..53) and
# would have blocked ~8% of outlet area — fixed.
# v0.53 (issue #2): the two pairs are pushed 2 mm further OUTWARD along the
# short axis (local Y = -5 / +30.6, was -3 / +28.6 = 5 mm past each long edge)
# so their holes clear the recess cutout. At the v0.53 anchor these land at
# PCB (16.5, 0) / (52.1, 0) / (16.5, -8) / (52.1, -8) — the 16.5 / 52.1 X
# columns sit 4.0 / 4.25 mm outside the cutout X edges (20.50 / 47.85), i.e. a
# ~2.5 / 2.75 mm FR4 web from each Ø3 hole edge to the cutout edge. With the
# module recessed, the zip ties now cross UNDER the module's protruding back
# (counts against the 5 mm back-side budget — physical check at next order).
# Y = -5 and Y = body_y + 5 = 30.6 (5 mm clearance past each long edge).
SEN66_ZIPTIE_LOCAL = [
    ("ZT1", 22.0, -5.0),
    ("ZT2", 22.0, 30.6),
    ("ZT3", 30.0, -5.0),
    ("ZT4", 30.0, 30.6),
]

# J3 (JST GH 6-pin board-side socket — SM06B-GHS-TB, horizontal SMD).
# Pin mapping: J3 is the positional MIRROR of the SEN6x Table 16 module
# pinout — 1=VDD, 2=GND, 3=SCL, 4=SDA, 5=GND, 6=VDD — because a straight
# flat GH lead reverses pin positions between two face-to-face polarized
# headers (issue #6). See the J3 block in _sch_sensors.py + CLAUDE.md
# Lesson 21; enforced by pipeline stage 19 check E.
# Placed in the SW pocket, in the same X column as the ZT1/ZT3 zip-tie holes
# (X=16.5), SOUTH of them (and south of the D1/Q1/F1 protection column) so
# the SEN66's ~50 cm flat lead gets a long, gentle bend from the module's
# connector (on the +X short edge at PCB (34.3, -33.2), the NORTH cutout edge)
# down and around into J3. v0.53-b (issue #2, user change order): moved from
# the old SE pocket (34, 31) to (16.5, 33.5) to open up cable-bend room. The
# cable mouth still faces WEST (rotation 90). Clearances re-measured against
# the ACTUAL emitted courtyards (J3 rot-90 courtyard half-extent = X 3.2 /
# Y 5.98 mm from the 6-pin 1.25 mm row):
#   - D1 (SMB, (17, 22.5) rot90) south courtyard edge +26.155; J3 north edge
#     +27.52 → 1.37 mm clear (≥1.0).
#   - R1 (0603, (12, 26.5) rot90) east courtyard edge +12.73; J3 west edge
#     +13.30 → 0.57 mm X gap (courtyards DISJOINT in X → no overlap).
#   - J1 east courtyard +9.15; J3 west edge +13.30 → 4.15 mm (and no Y overlap).
#   - flat chord +43.52; J3 south courtyard edge +39.48 → 4.04 mm clear.
#   - cutout west edge +20.50; J3 east courtyard edge +19.70 → 0.8 mm clear.
J3_X = 16.5   # v0.53-b (issue #2): user change order — align with ZT3's X
              #   (SEN66_ZIPTIE ZT3 lands at PCB X=16.5) so J3 sits in the
              #   ZT1/ZT3 column, giving the SEN66 lead a long sweeping bend.
J3_Y = 33.5   # v0.53-b: slightly south of the old +31 so the J3 north
              #   courtyard edge (+27.52, = 33.5 - 5.98) clears D1's south
              #   courtyard edge (+26.155) by 1.37 mm (≥1.0). Further south
              #   would crowd the chord (south courtyard edge +39.48 already).
J3_ROTATION = 90   # v0.53 (issue #2): rotated 90 (from 0) so the cable mouth
                   # (pad-side, native footprint "north"/-Y) points PCB -X
                   # (WEST). Under _sen66_local_to_pcb's rotation matrix a
                   # local -Y feature maps to PCB -X at rotation 90, i.e. the
                   # mouth turns from "up" to "left" — a 90° counter-clockwise
                   # turn in the board top view. Kept at 90 per the change
                   # order (no collision forces otherwise). (Pin NET order is
                   # unaffected by rotation — stage 19 check E stays valid.)

# J3 cable pass-through slot (v0.53, issue #2 follow-up — bench finding):
# with the SEN66 recessed into the cutout, the module's own GH receptacle
# sits BELOW the PCB plane, so the lead leaves the module on the back side
# and must return to the front face to reach J3. A second Edge.Cuts slot
# EAST of J3 lets the cable plug (JST GHR-06V housing, ~10.5 x 4.1 mm)
# pass through from below; the lead then loops west into J3's west-facing
# mouth. Same orientation as J3 (long axis along PCB Y, matching the
# rot-90 pin row), centred on J3_Y. The 5 mm FR4 web between J3 and the
# slot gives the flat lead room for the up-and-over service loop.
# Clearances (see tests/test_project_constants.py::test_j3_cable_slot_*):
#   - north: SEN66 recess cutout south edge +23.0 -> 5.0 mm web
#   - south: flat chord +43.498 -> 4.5 mm web
#   - west:  J3 east courtyard edge +19.70 -> 5.0 mm web (the gap below)
#   - far corner (29.7, 39.0) sits R=49.0 -> ~11 mm inside the R60 arc
_J3_COURTYARD_HALF_X = 3.2    # rot-90 courtyard half-extent (measured from
                              # the emitted J3 footprint — see J3_Y comment)
J3_CABLE_SLOT_GAP = 5.0       # FR4 web: J3 east courtyard edge -> slot west edge
J3_CABLE_SLOT_W = 5.0         # slot X extent (plug housing depth 4.1 + slack)
J3_CABLE_SLOT_L = 11.0        # slot Y extent (plug housing width 10.5 + slack)
J3_CABLE_SLOT_CORNER_R = 1.5  # rounded corners; >= 1.0 mm for a Ø2 internal mill
J3_CABLE_SLOT_X_MIN = J3_X + _J3_COURTYARD_HALF_X + J3_CABLE_SLOT_GAP   # 24.70
J3_CABLE_SLOT_X_MAX = J3_CABLE_SLOT_X_MIN + J3_CABLE_SLOT_W             # 29.70
J3_CABLE_SLOT_Y_MIN = J3_Y - J3_CABLE_SLOT_L / 2                        # 28.00
J3_CABLE_SLOT_Y_MAX = J3_Y + J3_CABLE_SLOT_L / 2                        # 39.00

# -----------------------------------------------------------------------------
# Board-id silk block (west pocket) — v0.53
# -----------------------------------------------------------------------------
# The NFC removal (issue #7) left the west pocket empty (the MIKROE-2462
# body shadow spanned X -40.16..-14.76, Y -16.51..+40.64). It now hosts
# the board identification block: name + version + the public repo URL
# (OAS_NAME_SHORT / OAS_VERSION_LINE / OAS_REPO_URL_SILK_LINES in
# _common.py) — so a physical board self-documents where its sources
# live. (v0.53-c first put a QR code here; replaced by plain text per
# user decision — the QR needed a filled-poly exemption in the stage-13
# silk lifter plus scan-polarity care, while text needs nothing.)
# Placement: block centred ON the horizontal axis of the central cable
# hole (Y = 0), X centred in the pocket. Pocket window on that axis:
# LD2410 body east edge -43.47 .. LED-ring west extent ~-14.8 (D15 at
# ring radius + its designator text) -> centre -29.0. Widest rows
# ("Open Ambient Sensor" / "open-ambient-sensor", 19 chars at the
# 1.0 mm min_text_height, ~1.36 mm/char stroke-font advance) span
# ~25.8 mm -> X -41.9..-16.1; margins ~1.6 mm to the LD2410 silk and
# ~1.5 mm to the ring's westmost courtyard. 5 rows at 2.4 mm pitch
# (Y -4.8..+4.8) sit well inside the pocket's Y range.
BOARD_ID_CENTER_X = -29.0
BOARD_ID_CENTER_Y = 0.0       # user spec: on the central hole's horizontal axis
BOARD_ID_ROW_PITCH = 2.4      # mm between the 5 text baselines (size 1.0)

# -----------------------------------------------------------------------------
# LD2410C PCB placement (J4 pin header + mechanical reference) — chunk #5b
# -----------------------------------------------------------------------------
# v0.53 (GitHub issue #9): the HLK-LD2410B was replaced by the HLK-LD2410C.
# Same radar, same 256000-baud protocol (same ESPHome `ld2410` component),
# but a completely different board: 22 x 16 mm carrying FIVE PLATED HOLES
# on a 2.54 mm pitch (Ø0.9 mm) instead of the -B's 35 x 7 mm strip with a
# 1.27 mm castellated edge. The -B edge was miserable to hand-solder (this
# project was burned by it twice), and both -B samples sourced for the
# prototype shipped with a permanently mute UART TX.
#
# MOUNTING: a plain 1x5 gold-pin header at 2.54 mm pitch (J4, stock KiCad
# `Connector_PinHeader_2.54mm:PinHeader_1x05_P2.54mm_Vertical`) is soldered
# into the OAS PCB; the module drops onto the protruding pins from above
# and is soldered on its own top face. The solder joints are BOTH the
# electrical and the mechanical retention — no cable, no bracket.
#
# ORIENTATION — the convention the pin order is DEFINED AGAINST (board-owner
# spec, 2026-07-21; see CLAUDE.md Lesson 20):
#   The module's two copper patch antennas face UP, AWAY from the OAS PCB
#   and toward the AK-N-94 perforated cover, because the radar must look
#   into the room. Viewed antenna-face-toward-the-observer with the pin row
#   along the module's NORTH edge — which is exactly the ordinary PCB top
#   view, looking down at the board — the pins run FROM LEFT (west):
#       1 = Tx, 2 = Rx, 3 = OUT, 4 = GND, 5 = VCC
#   (Hi-Link HLK-LD2410C manual V1.00, 2022-11-07, Table 1 / section 4.2;
#   pin 1 = Tx carries the SQUARE pad, pins 2..5 are round.) On the OAS PCB
#   that means the J4 hole row runs east-west along PCB +X with pin 1 at
#   the WEST end, and the module body extends SOUTH from the row.
#   This is the MIRROR of the -B order (1 = OUT .. 5 = VCC) — the reversal
#   is the whole point of the redesign, so the -B mapping must NOT be
#   carried over. A secondary web source (espboards.dev) lists the row as
#   "VCC, GND, TX, RX, OUT", which is the same row read from the far end;
#   the manual's Table 1 plus the square pin-1 pad settle it.
#
# J4 is the PHYSICAL DATUM (CLAUDE.md Lesson 22 corollary): the hole row is
# where the real module is forced to sit, so J4_PCB_X / J4_PCB_Y are the
# authored numbers and the body outline below is DERIVED from them. Never
# author the body anchor directly.
J4_PCB_X = -37.0             # mm — PCB X of pad 1 (Tx) at the WEST end of
                              # the row. Pads land at -37.00 / -34.46 /
                              # -31.92 / -29.38 / -26.84 (2.54 mm pitch).
J4_PCB_Y = +12.0             # mm — PCB Y of the pad row.
J4_PCB_ROTATION = 90         # degrees. Empirical stock-footprint rotation
                              # convention (unchanged from the -B era): a
                              # native pad at local (0, +k) lands at PCB
                              # (anchor_x + k, anchor_y) under rotation 90,
                              # so rotation 90 puts pad 1 AT the anchor
                              # (WEST end) and pad 5 at anchor_x + 10.16
                              # (EAST end) — the orientation the spec above
                              # requires. Enforced by pipeline stage 19
                              # check D together with the schematic net
                              # binding in _sch_sensors.py.

# ---- HLK-LD2410C body geometry (module-local mm) ----------------------------
# Local frame: origin at the body corner that is NORTH-WEST on the OAS PCB
# (the west end of the pinned long edge); local +X runs along the pin row,
# local +Y runs into the body. LD2410_ROTATION = 0, so local X/Y map
# straight onto PCB X/Y — no rotation bookkeeping (the -B needed 270°).
#
# SOURCES. Body 22.0 x 16.0 mm, pitch 2.54 mm and hole Ø0.9 mm are
# DATASHEET-STATED (manual V1.00 section 4.1 + Table 2). The pin-row inset
# from the pinned edge and the antenna-patch rectangle are MEASURED off the
# manual's Figure 5, which is genuinely to scale (its two independent
# mm/px scales agree to 0.1 % and the measured pad pitch reproduces the
# stated 2.54 mm to within 0.6 %) — Hi-Link dimensions neither of them.
# ⚠ RE-VERIFY WITH CALIPERS ON THE DELIVERED MODULE BEFORE THE NEXT PCB
# ORDER (issue #9 acceptance criterion). The numbers at risk and what they
# would cost if wrong:
#   - LD2410_PIN_ROW_INSET_Y (±0.15 mm): shifts the DERIVED body outline
#     0.15 mm north or south. The nearest neighbour on that axis is C11
#     (0.90 mm north of the body), so the error is absorbed.
#   - LD2410_PIN1_INSET_X: derived arithmetically from "row centred on the
#     22 mm edge" ((22 - 4x2.54)/2 = 5.92) and bracketed by the measured
#     end insets (6.02 / 5.84). NOT cosmetic — J4 is nailed to the PCB, so
#     this constant says where the PHYSICAL module sits relative to it. An
#     error moves the real module west, into the only tight clearance on
#     the board: 1.80 mm from the body corner to the edge of H2's M3 pan
#     head (true 2D distance). The module underside sits ~2.5 mm up and an
#     M3 pan head is ~2.4 mm tall, so there is NO vertical escape — that
#     lateral gap is load-bearing. A module whose row is off-centre by
#     >1.8 mm westward cannot be assembled with the H2 screw fitted, and
#     it would only be discovered at prototype assembly, after the boards
#     are paid for. THIS is the caliper measurement that matters most:
#     measure the pin-1 end inset and confirm the resulting west body edge
#     keeps clear of H2, not just that the silk looks right.
#   - LD2410_BODY_Z / the standoff budget: Hi-Link states NO thickness
#     anywhere and the module carries components on BOTH faces, so this is
#     the other number that could bite mechanically.
# The ELECTRICAL layer is independent of all of them: the pads come from
# the stock 2.54 mm footprint and their pitch is datasheet-stated.
LD2410_BODY_W = 22.0             # mm, local +X extent — the pinned LONG edge
                                  # (manual V1.00 section 4.1: "Module size:
                                  # 16mm x 22mm", Figure 5 dimensions 22.00
                                  # along the pin row).
LD2410_BODY_H = 16.0             # mm, local +Y extent — the SHORT edge; the
                                  # body runs SOUTH from the pin row.
LD2410_BODY_Z = 6.0              # mm, approx height above the OAS PCB:
                                  # ~2.5 mm gold-pin spacer + ~1.6 mm module
                                  # PCB + ~2 mm of top-face components.
                                  # NOT datasheet-backed (see the caliper
                                  # note above); well inside the 17 mm
                                  # front-side limit either way.
LD2410_PIN_PITCH = 2.54          # mm (datasheet-stated)
LD2410_PIN_COUNT = 5
LD2410_PIN1_INSET_X = (LD2410_BODY_W - (LD2410_PIN_COUNT - 1)
                       * LD2410_PIN_PITCH) / 2.0      # = 5.92 mm; the 5-hole
                                  # row is CENTRED on the 22 mm edge
                                  # (measured pin-1 / pin-5 end insets 6.02
                                  # and 5.84 mm bracket the ideal 5.92).
LD2410_PIN_ROW_INSET_Y = 1.42    # mm — pad-centre row to the pinned long
                                  # edge. MEASURED (±0.15), see above.
                                  # ⚠ Figure 5 carries a second "2.54mm"
                                  # callout drawn vertically near this
                                  # dimension; its extension lines land on
                                  # the silkscreen text and the antenna
                                  # ground pour, NOT on the pad row — it is
                                  # a duplicated pitch label, do not read it
                                  # as the inset.

# Antenna patches (local mm) — two identical microstrip patches on the top
# (antenna) face. Drawn dashed on F.Fab so the layout shows where the
# 24 GHz beam leaves the module and nothing tall is parked in front of it.
LD2410_ANTENNA_Y_MIN = 4.50      # from the pinned long edge (measured)
LD2410_ANTENNA_Y_MAX = 9.92
LD2410_ANTENNA_PATCH_X: tuple[tuple[float, float], ...] = (
    (3.28, 7.23),                 # west patch
    (14.83, 18.78),               # east patch
)

# ---- Silkscreen geometry (module-local mm) ----------------------------------
LD2410_SILK_INSET = 0.2          # F.SilkS body outline drawn 0.2 mm inside
                                  # the F.Fab body rectangle.
# The north (pinned-edge) silk line cannot be drawn across the connector:
# it would sit 0.16 mm from the J4 stock silk frame's own north edge
# (0.04 mm edge-to-edge after the 0.12 mm strokes) — a silk_overlap.
# It is therefore emitted as TWO CORNER STUBS that stop clear of the whole
# J4 footprint. Keep-out span in local X = pin 1 - 1.38 (the stock frame's
# pin-1 marker) .. pin 1 + 11.54 (the frame's far end), widened by
# LD2410_SILK_CONN_GAP on both sides. Same reasoning as the -B era U-shape
# and the MOD1 corner ticks: mark the corners, skip the congested span.
_J4_SILK_WEST_OF_PIN1 = 1.38     # stock PinHeader_1x05_P2.54mm_Vertical silk
_J4_SILK_EAST_OF_PIN1 = 11.54    # frame extents, relative to pad 1
LD2410_SILK_CONN_GAP = 0.5       # mm of clear board between stub end and
                                  # the J4 silk frame
LD2410_SILK_NORTH_STUB_X_END = (LD2410_PIN1_INSET_X - _J4_SILK_WEST_OF_PIN1
                                - LD2410_SILK_CONN_GAP)          # 4.04
LD2410_SILK_NORTH_STUB_X_START = (LD2410_PIN1_INSET_X + _J4_SILK_EAST_OF_PIN1
                                  + LD2410_SILK_CONN_GAP)        # 17.96

# ---- Placement on the OAS PCB -----------------------------------------------
# DERIVED from the J4 datum (see the Lesson-22 note above). With the -C body
# the module claims a 22 x 16 mm shadow instead of the -B's 7.6 x 35.6 mm
# strip, so it can no longer hug the west rim: the old strip spanned PCB
# X -51.09..-43.47 / Y -16.51..+19.05, straight across H2's X column. The
# new spot is the south-west pocket, EAST and SOUTH of the -B position
# (which is also where the board owner expected it to go).
#
# Body shadow on the OAS PCB (rotation 0, so local == PCB axes):
#   X  -42.92 .. -20.92   (anchor_x .. anchor_x + LD2410_BODY_W)
#   Y  +10.58 .. +26.58   (anchor_y .. anchor_y + LD2410_BODY_H)
#
# Clearance survey (all against the emitted courtyards / silk):
#   - H2 mounting hole (-47.63, +27.5), Ø3.8 NPTH, courtyard r=2.85 →
#     X -50.48..-44.78. Body west edge -42.92 → 1.86 mm clear, and 1.71 mm
#     to the rim of a Ø6 M3 pan head. The body must NOT reach over H2: the
#     module sits only ~2.5 mm up on its header, far below a screw head.
#     This is what stops the module moving further west.
#   - AQI LED ring, west extent: D14 courtyard X -13.40..-10.54 (Y
#     +9.19..+14.11), D15 courtyard X -12.25..-9.85. Body east edge -20.92
#     → 7.52 mm clear. This is what stops it moving further east.
#   - Board-id silk block (X -41.92..-16.08, Y -4.80..+4.80, text band to
#     +5.30): body north silk +10.78 → 5.48 mm, which is the strip the five
#     per-pin labels live in (see gen_silk_labels).
#   - J1 terminal block courtyard X -9.13..+9.12 and its mating-plug no-go
#     rectangle (X ≈ -8.2..+8.2): body east edge → >11.7 mm clear.
#   - R60 outline: body SW corner (-42.92, +26.58) sits at r=50.48 →
#     9.52 mm inside; the flat chord (+43.52) is 16.94 mm south of the body.
#   - Nothing at all is placed under the shadow (checked by the Z-clearance
#     guardrail in _postprocess.py, budget DAUGHTERBOARD_Z_CLEARANCE
#     ["LDR1"]). C11, the module's +5V decoupling cap, sits just NORTH of
#     the pin row and clear of the shadow — see gen_sensors_decoupling.
LD2410_ROTATION = 0              # degrees — the -C needs no rotation: its
                                  # pin row already runs along the module's
                                  # long axis, which is the OAS PCB's +X.
                                  # (The -B was mounted at 270°, standing
                                  # its 35 mm strip on end along PCB Y.)
LD2410_ANCHOR_X = J4_PCB_X - LD2410_PIN1_INSET_X        # -42.92 (DERIVED)
LD2410_ANCHOR_Y = J4_PCB_Y - LD2410_PIN_ROW_INSET_Y     # +10.58 (DERIVED)


def _ld2410_local_to_pcb(lx: float, ly: float) -> tuple[float, float]:
    """Transform a footprint-local LD2410C coordinate to PCB-local mm.

    Mirrors `_sen66_local_to_pcb`. With LD2410_ROTATION = 0 this is a
    pure translation by the (DERIVED) anchor, but the rotation matrix is
    kept generic so the module can be turned without touching callers.
    """
    a = math.radians(LD2410_ROTATION)
    cos_a, sin_a = math.cos(a), math.sin(a)
    rx =  cos_a * lx + sin_a * ly
    ry = -sin_a * lx + cos_a * ly
    return (LD2410_ANCHOR_X + rx, LD2410_ANCHOR_Y + ry)


# -----------------------------------------------------------------------------
# ESP32-C6 DevKitM-1-N4 — PCB shadow reservation
# -----------------------------------------------------------------------------
# The devkit is a daughterboard mounted on FEMALE pin sockets on the
# OAS PCB. The board sits ~3-7 mm above the PCB on the
# standoff of its pin headers, so SMD components on the OAS PCB CAN be
# placed under its shadow (within the standoff Z budget of ~3-5 mm).
#
# This chunk just RESERVES the shadow area with a mechanical-reference
# footprint (F.Fab body outline + F.SilkS marker + pin-row hints + labels).
# The actual electrical female pin sockets land in chunk #7 (PCB routing).
#
# Layout (v0.15.6; MIKROE-2462 NFC daughterboard removed in issue #7 —
# its former shadow, body X=-38.16..-14.76 / Y=-16.51..+40.64, is free
# board area now):
#
#   ESP32-C6 DevKitM-1-N4
#   body: 48.26 × 25.4 mm (+ 13.20 × 5.37 mm antenna tab, west)
#   anchor (-30.465, -24.70)   [v0.53 — see ESP32_ANCHOR_X comment]
#   body X=-30.465..+17.795
#   body Y=-50.10..-24.70
#   center X = -6.335
#   horizontal at TOP-CENTER
#   antenna LEFT (-X)
#   USB-C RIGHT (+X)
#
# SEN66 (right side, anchor +21.5/+22.0) — see per-constant comments
# below for clearance breakdowns.

# Dimensions per Espressif official dimensions drawing
# https://dl.espressif.com/dl/schematics/esp32-c6-devkitm-1-dimensions.pdf
# Body 25.40 × 48.26 mm. Pin headers 2×1×15 P2.54 mm, row spacing 22.86 mm.
# Pin block is OFFSET along the long axis: the drawing dimensions the
# USB-C-side inset directly (last pin → USB short edge = 11.125 mm), so
# pin 1 sits 48.26 − 14×2.54 − 11.125 = 1.575 mm from the antenna short
# edge. The two rows are symmetric about the long axis.
# HISTORY (v0.53 post-#3 review): the offset was recorded as 5.37 mm from
# v0.15 until the issue-#3 review — a misattribution of the ANTENNA TAB
# PROTRUSION dimension (the drawing's vertical "5.37" measures the module
# sticking out past the board edge, NOT the pin-1 inset), ratified for
# months by a circular sum-check (7.33 was back-derived, never read from
# the PDF). The bench symptom was real: the physical module sat 3.795 mm
# further toward the USB/caps side than the drawn shadow — which is WHY
# the C1/C3/C4 caps blocked seating (issue #3) despite the drawing
# showing clearance. Verified against the re-rendered PDF (Lesson 6).
ESP32_BODY_W = 25.4
ESP32_BODY_L = 48.26
ESP32_BODY_Z = 8.6                # approx Z above OAS PCB (module + std-off)
# ESP32-C6-MINI-1 PCB-antenna tab: the module's antenna section overhangs
# the devkit PCB's antenna short edge. BOTH numbers are EXTRACTED from the
# Espressif dimensions drawing (esp32-c6-devkitm-1-dimensions.pdf, re-rendered
# and read directly — Lesson 6): the "13.20" dimension spans the antenna
# rectangle width (= ESP32-C6-MINI-1 module width), and the "5.37" dimension
# runs from the board's antenna short edge UP to the tab tip = the protrusion.
# (Reviewer-confirmed 13.20 / 5.37, cross-checked against the same PDF.)
# CAUTION: 5.37 belongs to THIS tab dimension ONLY — it was historically
# ALSO (wrongly) recorded as ESP32_PIN_START_OFFSET; see the HISTORY note
# above. The tab is centred on the body width.
ESP32_ANTENNA_TAB_W = 13.20         # mm, along the short (25.4 mm) axis — PDF
ESP32_ANTENNA_TAB_PROTRUSION = 5.37  # mm, past the antenna short edge — PDF
ESP32_PIN_ROW_INSET = 1.27         # = (25.40 - 22.86) / 2
ESP32_PIN_PITCH = 2.54
ESP32_PIN_COUNT_PER_ROW = 15
ESP32_PIN_START_OFFSET = 1.575     # distance from antenna short edge (LIB
                                    # Y=0) to pin 1 = 48.26 − 14×2.54 −
                                    # 11.125 (the PDF dimensions the
                                    # USB-side inset, 11.125, directly).
                                    # Was 5.37 (the antenna-tab protrusion,
                                    # misattributed) until the issue-#3
                                    # review — see HISTORY above.

# Placement (v0.15): ESP32 HORIZONTAL, UPPER-LEFT. User instruction
# (translated): "ESP far down and to the left" — historically bounded from below by the
# (since-removed, issue #7) NFC daughterboard sharing LD2410's Y band.
# ESP32 stays horizontal, shifted LEFT, dropped as far down as the
# then-present NFC top edge allowed. Body X range leaves a 2.5 mm gap
# to LD2410's right edge at X=-39.66 and 12.4 mm to SEN66's left edge
# at X=+23.5. Helper rotation 90° unchanged (body lies down 48.26 × 25.4).
ESP32_ANCHOR_X = -30.465           # v0.53 (issue #3 + its review + live fit
                                    # check): the PHYSICAL datum is the J5/J6
                                    # socket rows — pin 1 at PCB X = anchor +
                                    # offset = -28.89, a NET 6.5 mm WEST of the
                                    # v0.51 boards' -22.39. History of the
                                    # datum: the user first measured a 7.5 mm
                                    # west move (pin 1 -29.89), then after a
                                    # live fit check on the physical assembly
                                    # trimmed it 1.0 mm back EAST for west-side
                                    # safety margin — the surplus toward the
                                    # THT caps / SEN66 was ample, so 6.5 mm
                                    # nets more slack where it matters. When
                                    # the pin-1 offset was corrected 5.37 →
                                    # 1.575 (see HISTORY above), the anchor
                                    # became datum − 1.575 = -30.465; the
                                    # anchor is DERIVED, the sockets are the
                                    # truth.
                                    # Body X range -30.465..+17.795, center
                                    # X = -6.335. Clearances (real module):
                                    #   - C3 Ø8 radial can west rim +21.75 −
                                    #     body east +17.795 = 3.955 mm → the
                                    #     module seats fully next to the caps.
                                    #   - SEN66 cutout west edge +20.50 −
                                    #     body east +17.795 = 2.705 mm.
                                    #   - body NW corner (-30.465, -50.10):
                                    #     r=58.636 → 1.364 mm INSIDE R60 —
                                    #     NO overhang.
                                    #   - antenna tab tip X=-35.835; far corner
                                    #     (-35.835, -44.00) r=56.746 → 3.25 mm
                                    #     INSIDE R60.
                                    # F.Fab carries the full true outline (body
                                    # + tab); F.SilkS carries four corner
                                    # L-ticks (a full silk rect would cross
                                    # the U1 lead-pad ends X -31.55..-28.05
                                    # and the J5/J6 frame ends X -30.22 on the
                                    # west, and skirts the C2 pad column
                                    # (~X +17.6) on the east — see the MOD1
                                    # block in _footprints_placement.py).
ESP32_ANCHOR_Y = -24.70            # v0.15.3: +2 mm DOWN from v0.15.2's
                                    # -26.70. Body Y range -50.10..-24.70.
                                    # Top edge 3.00 mm above H3 hole top
                                    # at Y=-53.1 (was 1.0 mm). NW corner
                                    # clearance vs the R60 outline: see the
                                    # ESP32_ANCHOR_X comment (1.364 mm
                                    # inside at the v0.53 anchor).
                                    # v0.18: REVERTED the v0.17 1.5 mm
                                    # north-shift (was -26.20) back to
                                    # the pre-v0.17 -24.70 value. J1
                                    # moved to the SOUTH side of the
                                    # cable hole in v0.18, so the
                                    # central north strip no longer
                                    # needs to make room for J1's
                                    # courtyard depth.
ESP32_ROTATION = 90                # KiCad rotation applied to helper output

# (MIKROE-2462 NFC daughterboard constants removed in issue #7 — the NFC
# feature left the design entirely. Former shadow: X=-40.16..-14.76,
# Y=-16.51..+40.64, west of the LED ring / south of LD2410.)


# -----------------------------------------------------------------------------
# J4 (the LD2410C pin header) lives in the LD2410C block ABOVE — it is the
# physical datum the module body is derived from, so the two must be read
# together. See J4_PCB_X / J4_PCB_Y / J4_PCB_ROTATION there.
# -----------------------------------------------------------------------------

# -----------------------------------------------------------------------------
# J1 PCB placement (v0.18; supersedes v0.17) — 24 V Phoenix MSTBA terminal block
# -----------------------------------------------------------------------------
# v0.17 placed J1 in the NORTH-of-cable-hole zone (replacing AQI LED D20).
# v0.18 FLIPS J1 to the SOUTH-of-cable-hole zone (replacing AQI LED D14
# instead): the south side has more open space because ESP32 occupies the
# north corridor, while the south corridor between the cable hole and the
# chord-edge cutouts is largely empty (the chord cutouts C3/C4/C5 are
# narrow X strips that don't block the central Y=0..+25 region). D20 is
# restored; D14 is now the missing LED. The ESP32 north-shift made in
# v0.17 is reverted.
#
# The 24 V supply cable enters from the rear of the enclosure (electrical
# wall box behind the unit), passes through the central hole, bends ~90°
# on the front side, and enters the terminal-block clamp from its NORTH
# face (clamp opening now faces the cable hole from the south side).
#
# Footprint: Connector_Phoenix_MSTB :
#   PhoenixContact_MSTBA_2,5_3-G-5,08_1x03_P5.08mm_Horizontal
# (matches the schematic's "Phoenix_MSTBA_2,5/3-G-5,08" library symbol).
# Stock footprint geometry (footprint-local):
#   - Pin 1 at (0, 0), pin 2 at (+5.08, 0), pin 3 at (+10.16, 0)
#   - F.Fab body: X = -3.54..+13.70, Y = -2.00..+10.00
#   - Courtyard:  X = -4.04..+14.21, Y = -2.50..+10.50
#   - Cable-entry face on the body's LIB +Y side (body bulk side,
#     with terminal-screw indicators at LIB Y = +8.61..+10.11 marking
#     each pin's cable insertion guide). The LIB -Y side (Y = -2.31..
#     -2.91) carries the small pin-1 indicator triangle but no cable
#     features — that's the PCB-edge / pin-solder side.
#
# Placement (v0.18, south flip): PCB anchor (pin 1 PCB position) is offset
# so pin 2 (middle pin) lands at PCB X = 0. Rotation 180° places the
# cable-entry face (LIB +Y, the side carrying the trapezoidal cable-
# insertion indicators per pin) on PCB -Y (NORTH, facing the cable hole),
# and the body's +Y bulk (terminal screws) extends NORTH from the pin
# row toward the cable hole. The pin solder side (LIB -Y, Y = -2..0)
# maps to PCB +Y (SOUTH), where it occupies 2 mm of the gap between the
# pin row and the chord cutouts.
#
# Clearance budget (rotation 180°, pin 2 centred at PCB X=0):
#   - Courtyard PCB Y range = [pin_y − 10.5, pin_y + 2.5] (13 mm depth)
#   - Courtyard PCB X range = [−9.13, +9.12]
#   - At pin_y = +22.4:
#       Courtyard Y = [+11.90, +24.90]
#       Nearest LED-courtyard south corner (D13/D15 at PCB Y = +11.67):
#         0.23 mm clearance to J1 courtyard north edge.
#       Cutout C3 north edge at PCB Y = +28.998: 4.10 mm clearance to
#         J1 courtyard south edge.
#       SEN66 body west edge at PCB X = +23.5: 14.38 mm X clearance to
#         J1 courtyard east edge at PCB X = +9.12.
#       J3 (SEN66 socket) courtyard west edge at PCB X = +30.02:
#         20.90 mm X clearance.
#
# Cable bend geometry: the cable enters the connector through the NORTH
# (cable-hole-facing) face at PCB Y = pin_y − 10.11 = +12.29 (F.SilkS
# edge) or pin_y − 10.5 = +11.90 (courtyard edge). The cable hole's
# SOUTH edge sits at PCB Y = +6 (Ø12 mm hole, radius 6). Effective
# horizontal travel for the cable bend: 12.29 − 6.00 = 6.29 mm. Each
# 1.5 mm² conductor enters its own screw clamp; the three conductors
# fan out from the hole exit, so each bends independently rather than
# as a bundle. A single 1.5 mm² insulated wire (OD ~3 mm) has a typical
# minimum bend radius of ~10 mm — slightly larger than the available
# travel, so the cable will bend somewhat aggressively at the hole
# exit. Acceptable for a low-flex installation (the cable is fixed at
# both ends and is not manipulated after assembly). Identical magnitude
# to the v0.17 north-side placement (mirror geometry).
J1_PCB_X = +5.08             # PCB X of pin 1. With rotation 180°, pin 2
                              # (middle) lands at PCB X = J1_PCB_X −
                              # 5.08 = 0. Pin row spans PCB X = +5.08
                              # (pin 1, +24V) .. −5.08 (pin 3, PE),
                              # centred on the PCB X axis and aligned
                              # with the LED slot at θ=90° now vacated
                              # (D13 at 8x45° ring; was D14 at 12x30° ring).
                              # Note: pin 1 (+24V) lands on PCB +X (east
                              # side); compare to v0.17 where pin 1 sat
                              # on -X (west). The user sees pins in
                              # left-to-right order PE, GND, +24V when
                              # looking at the south face (cable insert
                              # side).
J1_PCB_Y = +32.0             # PCB Y of pin row (footprint-local Y = 0).
                              # v0.45: 0.4 mm north (+32.4 -> +32.0). J1.1,
                              # the easternmost 24 V THT pad, sat only
                              # 2.98 mm diagonally from J9.1 (Qwiic SMD
                              # pad) — a JLCDFM "tht to smd" warning
                              # (>3.05 mm rule). +0.4 mm north lifts the
                              # gap to ~3.3 mm. J1 has 7.8 mm of open
                              # space north (nearest is LED D12), so the
                              # move is fully unconstrained.
                              # v0.41-followup-2 (2026-05-19): +5 mm south
                              # to widen the no-go rectangle between J1's
                              # mating face and the central cable hole, so
                              # the cable-terminal plug has more clearance.
                              # Y was +27.4 since the pre-routing rework.
                              # With rot 180, courtyard extends NORTH from
                              # pin row; body bulk (terminal screws)
                              # recedes from cable hole. J10 chord cutout
                              # C3 may intersect — accept temporarily.
                              # See clearance budget above for derivation.
                              # At pin_y = +22.4 with rot 180:
                              #   J1 courtyard Y = (+11.90, +24.90)
                              #   J1 F.SilkS south edge (incl. pin-1
                              #     indicator triangle at LIB Y = -2.91
                              #     → PCB Y = +25.31) vs C3 cutout
                              #     north edge at PCB Y = +28.998:
                              #     3.69 mm clearance.
                              #   J1 F.SilkS north edge at PCB Y = +12.29
                              #     vs D13/D15 south F.Fab corner at
                              #     PCB Y = +11.67: 0.62 mm clearance.
J1_PCB_ROTATION = 180        # Rotation 180° places the cable-entry face
                              # of the body (LIB +Y) on PCB -Y (north,
                              # facing the cable hole). Pin 1 (+24V) at
                              # PCB +X (east), pin 3 (PE) at PCB -X
                              # (west).

# -----------------------------------------------------------------------------
# J9 — Qwiic / Stemma QT JST SH 4-pin horizontal SMD socket (v0.19)
# -----------------------------------------------------------------------------
# J9 lives in the C2 case-wall opening — the RJ45 / Ethernet-jack cutout in
# the AK-N-94 wall (X +1.1..+16.8, 15.7 mm wide, clipped at the chord). The
# C2 X range was mirror-corrected about X=0 — the source DXF is a bottom-of-
# enclosure view, so J9 / C2 belong on the +X (right) side of the board.
#
# Stock JST_SH_SM04B-SRSS-TB footprint: a 1.0 mm-pitch signal pad row
# (3 mm total width) plus two MP mech-pin tabs anchoring the body; body
# courtyard ~7.8 mm wide. The connector mouth (cable-entry slot) is on the
# pad side and faces the chord (+Y) so the cable plugs in from outside the
# case. J9_PCB_Y and J9_PCB_ROTATION are unaffected by the X mirror.
#
# Placement (routing-rework relocation): J9 moved OFF the C2 chord-side
# wall cutout and INTERNAL, east of the J10 recovery header. An external
# Qwiic cable threaded through the AK-N-94 wall cutout conflicts with
# design Pillar #2 (aesthetic acceptability — no exposed wiring); the
# Qwiic / Stemma QT expansion port is realistically an INTERNAL header
# used only when a future daughterboard is added inside the enclosure, so
# the connector belongs internal. The former cutout position also left
# the J9 +3V3 / SDA / SCL trio unroutable (Freerouting could not escape
# the chord-edge corridor). New anchor (+17.0, -19.5): courtyard spans
# X +13.08..+20.92, Y -22.81..-16.19 — 1.6 mm clear of the "J10 flash"
# board-silk label, 2.3 mm to the SEN66 zone west edge, 1.36 mm to the
# J5 courtyard. Recovers the J9 +3V3/SDA/SCL trio for the autoroute.
J9_PCB_X = +16.0             # PCB X — internal, east of the J10 header.
                              # v0.53 (issue #3): nudged 1.0 mm WEST (was
                              # +17.0). The east MP mounting-ear copper edge sat
                              # at +20.40 and its COURTYARD reached +20.90; with
                              # SEN66_CUTOUT_MARGIN_W restored to 1.0 the cutout
                              # west edge is +20.5, which at +17.0 left the MP
                              # copper 0.10 mm to the edge (DRC violation) and
                              # the courtyard 0.20 mm INSIDE the cutout. At
                              # +16.0 the MP copper east edge is +19.40
                              # (1.10 mm copper-to-edge) and the courtyard east
                              # edge +19.90 (0.60 mm clear) — both with real
                              # margin. Neighbours OK: ZT3 (16.5, -8) is
                              # 11.5 mm south, the DevKit south edge is at
                              # -24.70 (5.2 mm north of J9).
J9_PCB_Y = -19.5             # PCB Y — internal row, north of the J5 socket
J9_PCB_ROTATION = 0          # orientation unchanged from prior C5 placement

# -----------------------------------------------------------------------------
# J10 — Native-USB recovery header (v0.19) — DNP 6-pin 2.54 mm THT
# -----------------------------------------------------------------------------
# J10 sits in the C3 case-wall cutout (X +4.9..+13.9, Y +28.998..+43.5,
# 9 × 14.5 mm). Stock `PinHeader_1x06_P2.54mm_Vertical` footprint:
#   - Pad 1 (rectangle) at LIB (0, 0), pads 2..6 at LIB (0, +n*2.54)
#     for n in 1..5. Pad row total 12.7 mm long in LIB +Y direction.
#   - Body silk X = -1.38..+1.38, Y = +1.27..+14.08
#   - Body courtyard X = -1.77..+1.77, Y = -1.77..+14.47
#
# Desired layout: pin 1 (rect-pad marker, easy to identify by eye when
# using a pogopin jig) sits at the chord side. Cable / pogopin jig
# enters from outside the case at PCB +Y. So we want LIB +Y (pins 2..6
# pad row direction) to map to PCB -Y (away from chord, into PCB
# interior), meaning rotation 180°.
#
# With rotation 180° (LIB +Y → PCB -Y):
#   - Pad 1 at LIB (0, 0)        → PCB (anchor_x, anchor_y)
#   - Pad 2 at LIB (0, +2.54)    → PCB (anchor_x, anchor_y - 2.54)
#   - …
#   - Pad 6 at LIB (0, +12.7)    → PCB (anchor_x, anchor_y - 12.7)
#   - Body extents: PCB X = anchor_x - 1.38..anchor_x + 1.38;
#                   PCB Y = anchor_y - 14.08..anchor_y - 1.27
#   - Courtyard:   PCB X = anchor_x - 1.77..anchor_x + 1.77;
#                  PCB Y = anchor_y - 14.47..anchor_y + 1.77
#
# C3 cutout X = +4.9..+13.9, Y = +28.998..+43.5. Centre header on
# cutout midpoint X = +9.4. Pad 1 (south, closest to chord) at
# anchor_y = +41.5 → pad outer edge at PCB Y = +42.35 (pad radius 0.85,
# circle diameter 1.7 mm), 1.17 mm clear of the chord at +43.5 (passes
# min_copper_edge_clearance 0.3 mm). Pad 6 at PCB Y = +28.8 — slightly
# north of the cutout north edge (+28.998). That's intentional — pin 6
# (BOOT, the least frequently accessed in a recovery scenario) extends
# beyond the cutout into the PCB-side keepout-free region, where the
# silk label can describe what it is.
#
# Wait — actually we want ALL 6 pads ACCESSIBLE through the cutout.
# Re-anchor: pad 1 at anchor_y = +42.0, pad 6 at anchor_y - 12.7 = +29.3.
# Pad 6 inside cutout? +29.3 > +28.998 → YES, all pads inside cutout.
# Pad 1 outer edge at +42.85 → 0.65 mm clear of chord. OK.
J10_PCB_X = -10.96            # PCB X of pad 1 (west end). Pre-routing
                              # rework 3: switched to HORIZONTAL on the
                              # transverse axis 3.5 mm south of J5 row
                              # (Y=-25.97). Pad row spreads east at
                              # 2.54 mm pitch: pad 6 at PCB X = -10.96 +
                              # 5*2.54 = +1.74. Centred roughly on J5
                              # span (X ∈ [-22.39, +13.17], midpoint
                              # ≈ -4.61). J5 silk designator label sits
                              # at PCB X=-17.02 (J5 row anchor + 5.37),
                              # 4.79 mm west of J10 body silk west edge
                              # (anchor + (-1.27) = -12.23 at rotation 90)
                              # → no overlap.
J10_PCB_Y = -21.0            # PCB Y of pad row. 4.97 mm south of J5 row
                              # A (Y=-25.97). v0.43: nudged 1 mm NORTH
                              # (from -20.0) so the per-pin F.SilkS labels
                              # placed south of the row clear LED D17 of
                              # the AQI ring.
J10_PCB_ROTATION = 90        # LIB +Y → PCB +X (horizontal pad row east).
                              # Rotation 90 swaps the dict half-extent
                              # tuple (1.5, 7.6) → effective (7.6, 1.5);
                              # the Z-clearance check handles this via
                              # the rotation flag captured by
                              # _parse_footprint_placements.

# -----------------------------------------------------------------------------
# J2 — UART/Boot recovery header (DNP), 1x06 P2.54 mm
# -----------------------------------------------------------------------------
# v0.43: relocated from the cramped NW corner to the free west pocket, and
# rotated HORIZONTAL (pad row along PCB +X, like J10). The cramped NW corner
# could not host printed F.SilkS per-pin labels; this pocket can. C2 and C3
# were evicted from it (see gen_power_pcb_footprints). With rotation 90 the
# 1x06 row runs +X from pin 1 (west) to pin 6 (east). Per-pin signal labels
# go on F.SilkS just NORTH of the row (gen_silk_labels).
# The pocket was originally framed as "north of the LD2410" — that framing
# died in v0.53 / issue #9 when the LD2410C moved to the south-west pocket
# (LD2410_ANCHOR_* above). J2 stayed put: the strip it occupies is simply
# free board now, ~4 mm south of the J5 socket row.
J2_PCB_X = -51.0             # PCB X of pad 1 (west end); row spans
                              # -51.0..-38.3 (6 pins, 2.54 mm pitch).
                              # Placed east of the pocket's west end so the
                              # pin-1 per-pin label clears the curving west
                              # board edge.
J2_PCB_Y = -21.0             # PCB Y of the pad row.
J2_PCB_ROTATION = 90         # LIB +Y → PCB +X (horizontal pad row east).

# -----------------------------------------------------------------------------
# Connector pin maps — single source of truth for per-pin silkscreen labels
# -----------------------------------------------------------------------------
# Each dict maps a 1-based pin number to the short label printed next to that
# pad on the PCB. The PCB silkscreen generator (gen_silk_labels) and the
# schematic generators consume the SAME dict, so a silk label can never drift
# from the netlist. Verified against the schematic sub-sheets:
#   J1     — _sch_power.py    (J1.1 VIN / J1.2 GND / J1.3 PE)
#   J2     — _sch_mcu.py      (UART/Boot recovery header)
#   J9     — _sch_io.py       (standard Qwiic: GND / +3V3 / SDA / SCL)
#   J10    — _sch_io.py       (native-USB recovery header)
#   J4     — _sch_sensors.py  (HLK-LD2410C module row, see below)
J1_PIN_MAP: dict[int, str] = {1: "24V", 2: "GND", 3: "PE"}
J2_PIN_MAP: dict[int, str] = {1: "+3V3", 2: "GND", 3: "TX", 4: "RX",
                              5: "EN", 6: "BOOT"}
# J4 — HLK-LD2410C. v0.53 (issue #9): every one of the five holes is
# labelled, not just the row ends — the -C is a hand-soldered module on a
# plain 2.54 mm header, so an assembler wants to read each pin off the
# board. The strings are the MODULE's own silkscreen (Tx / Rx / OUT / GND /
# VCC, printed left-to-right on its antenna face), so the board silk lines
# up 1:1 with what is printed on the part being fitted. NOTE the deliberate
# mismatch with the NET names: J4 pin 1 "TX" is the module's transmitter
# and therefore lands on the MCU-centric net LD2410_UART_RX, and pin 2 "RX"
# on LD2410_UART_TX (see _sch_sensors.py and CLAUDE.md Lesson 20).
J4_PIN_MAP: dict[int, str] = {1: "TX", 2: "RX", 3: "OUT", 4: "GND",
                              5: "VCC"}
J10_PIN_MAP: dict[int, str] = {1: "GND", 2: "+3V3", 3: "USB-", 4: "USB+",
                               5: "EN", 6: "BOOT"}

# Module socket end-pin signal names — printed at the EXTREME pads of each
# daughterboard row so the module can be oriented during hand-assembly.
# Signal names (not bare pin numbers) are used: they tell the assembler at
# a glance which way round the module goes. Only the first + last pad of a
# row carry a label (see gen_silk_labels). Keyed by footprint pad number.
# Used for J5/J6 only — J4 carries a full per-pin map (J4_PIN_MAP above)
# since v0.53 / issue #9.
#   ESP32-C6-DevKitM-1 — verified vs _lib_symbols.ESP32C6_DEVKITM1_PINS:
#     J5 = module header J1 (pad 1 = 3V3 … pad 15 = GND)
#     J6 = module header J3 (pad 1 = GND … pad 15 = GND — both rails GND
#          at the J3 header ends; J5's 3V3/GND orients the module)
J5_END_SIGNALS: dict[int, str] = {1: "3V3", 15: "GND"}
# v0.53 (issue #3): J6's WEST end (pin 1) label dropped — after the -7.5 mm
# DevKit move it fell over the SW board arc and could not be placed clear of
# both the J6 socket silk frame and the outline. Both J6 ends were "GND"
# (no orientation value; J5's 3V3/GND ends already orient the module), so only
# the roomy EAST end is labelled.
J6_END_SIGNALS: dict[int, str] = {15: "GND"}

# Polarity-sensitive designators — components whose orientation matters and
# which therefore MUST carry a polarity / pin-1 silkscreen mark. Consumed by
# pipeline/oas/21_check_polarity_silk.py, which fails the build if any of
# these footprints loses its F.SilkS polarity primitive.
#   D1/D2/D3 — diodes (TVS / Schottky / Zener): stock cathode bar
#   Q1       — AO3401A P-MOSFET (SOT-23): stock pin-1 mark
#   U1/U2    — buck ICs (TO-263-5 / SOT-583): stock pin-1 mark
#   C1/C3/C4 — polarized radial electrolytics: stock "+" / pad-1 mark
#   D11..D18 — SK6812-SIDE LEDs (oas custom footprint): pin-1 dot
#              (D13 is skipped at the J1 cable slot — not placed).
POLARIZED_DESIGNATORS: frozenset[str] = frozenset({
    "D1", "D2", "D3", "Q1", "U1", "U2", "C1", "C3", "C4",
    "D11", "D12", "D14", "D15", "D16", "D17", "D18",
})

# -----------------------------------------------------------------------------
# AQI status LED ring — 8 x SK6812-SIDE side-emit addressable RGB (45 deg pitch)
# -----------------------------------------------------------------------------
# Eight side-emit RGB LEDs (one skipped at the J1 cable-area position
# leaves seven placed) on a Ø26 mm pitch circle around the central
# Ø12 mm cable hole. Each LED radiates LIGHT RADIALLY OUTWARD into the
# AK-N-94 perforated cover where it scatters and reads as a soft glowing
# halo (no per-perforation hot-spot dotting). Side-emit geometry chosen
# over top-emit after a research pass on the diffuse-ring options.
#
# LED chip: SK6812 SIDE-A (Shenzhen Normand / OPSCO Optoelectronics).
# Package 4.0 (L) × 1.6 (W) × 2.0 (H) mm. Pinout 1=DIN, 2=VDD, 3=DOUT,
# 4=GND (verified against Normand 2018 rev 01 + OPSCO 2021 rev A/1
# datasheets; land pattern from EasyEDA C5378721 — see SK6812SIDE_PADS).
# See EXTERNAL_MODULES['SK6812-SIDE'] entry above for the verified part spec.
#
# Geometry:
#   - 8 LEDs at θ = 0°, 45°, 90°, 135°, 180°, 225°, 270°, 315° (KiCad-screen
#     +Y is down, so θ=0 is at PCB +X, θ=90 is at PCB +Y / SOUTH, etc.)
#   - LED center at (R·cos θ, R·sin θ) with R = LED_RING_RADIUS.
#   - Body local frame: +X = long axis (pad row); +Y = short axis pointing
#     toward the pad-row face (away from emission). The emission face is
#     at body-local -Y. To make each LED's emission face point radially
#     OUTWARD, we set its KiCad rotation R = (90 - θ) mod 360 so that
#     body-local (0, -1) maps to PCB (cos θ, sin θ).
#   - Daisy-chain order: D11 at θ=0, D12 at θ=45, … D18 at θ=315.
#     D18 DOUT terminates open (NeoPixel chains do not loop back).
#   - One 100 nF 0402 decoupling cap (C20…C27) per LED, placed adjacent
#     to the LED's VDD pad on the PCB-interior side of the ring.
#
# Why 45° pitch and not 30°: SMT assembly machines orient parts in
# standard multiples (0/45/90/135 deg); non-standard angles (30/60/etc.)
# can add per-part placement overhead at JLCPCB. Going from 12 LEDs
# at 30° to 8 LEDs at 45° trades 4 LEDs (negligible AQI-halo visual
# difference at this radius) for assembly simplicity. Audit-19
# (2026-05-19).
#
# LED_RING_RADIUS = 13.0 mm (pre-routing rework: bumped from 11.0 → 13.0
# to free up the cable-hole / centre routing channel). LED centres on
# a Ø26 mm pitch circle. Inner-most LED body edge at R = 12.2 mm (body
# half-extent 0.8 mm radially); 6.2 mm radial clearance to the Ø12 mm
# cable hole edge at R=6. Outer-most LED body edge at R = 13.8 mm.
# Chord distance between adjacent 45° LEDs: 2·R·sin(22.5°) = 9.95 mm,
# giving 2.98 mm gap per side of the 4 mm LED body (was 1.37 mm at 30°).
LED_RING_RADIUS = 13.0    # v0.41 2026-05-19 (rev 3): back to 13.0 base after
                            # user request. D12 (i=1, theta=45°) and D14 (i=3,
                            # theta=135°) get a per-index override to R=15 mm
                            # (see LED_RING_RADIUS_OVERRIDE below) — these two
                            # LEDs sit closest to the J1 24 V terminal block
                            # on the chord side; at R=13 their bodies would
                            # protrude into the J1 mating-plug clearance zone.
LED_RING_RADIUS_OVERRIDE = {
    0: 11.0,    # D11 — mirrored with D15 (also R=11). User wanted radial
                # symmetry on the east-west axis through the ring centre,
                # since D15 was forced to R=11 by the (since-removed,
                # issue #7) MOD2 silk constraint and we don't want the
                # silk-labelled reference LED (D11) to look bigger than
                # its opposite-axis counterpart.
    1: 16.5,    # D12 — bumped 15 → 16.5 (v0.41-followup-2). At R=16.5 cap C21
                # mask west edge at PCB X=+8.745 leaves 0.21 mm clearance for
                # a silk-no-go vertical line at PCB X=+8.50. Historical upper
                # bound R ≤ 16.48 came from D14 pin-1 dot vs the (since-
                # removed, issue #7) MOD2 silk east edge; 16.5 kept as the
                # known-good routed value.
    3: 16.5,    # D14 — bumped 15 → 16.5. Mirror of D12.
    4: 11.0,    # D15 — pulled INWARD historically to clear the (since-
                # removed, issue #7) MOD2 / MIKROE-2462 silk east edge.
                # R=11 kept: the value is baked into the v0.50 routing
                # snapshot; nothing forces it back out to 13.
}
LED_RING_COUNT = 8
LED_RING_THETA_START_DEG = 0.0       # first LED (D11) sits on PCB +X axis
LED_RING_THETA_STEP_DEG = 360.0 / LED_RING_COUNT   # = 45°

# J1 (24 V terminal block) sits on the SOUTH side of the cable hole
# with courtyard Y ∈ [+11.9, +24.9] mm — directly colliding with the
# LED slot at θ=90° (PCB (0, +13)). At 45° pitch that slot is index
# i=2, so we skip i=2 (was i=3 at 30° pitch). Skipped designator
# becomes D13 (and its decoupling cap C22). Daisy-chain wires the
# schematic generator emits already skip routing across this gap.
# Final ring: 7 LEDs (D11, D12, D14..D18) + 7 caps (C20, C21, C23..C27).
LED_RING_SKIP_INDICES = (2,)         # i=2 → D13 (and C22) at θ=90°

# Decoupling cap radial offset from LED centre: cap sits ~3.4 mm radially
# INWARD from the LED centre (so total radius = LED_RING_RADIUS - 3.4 =
# 7.6 mm). At inner cap edge (R = 7.6 - 0.5 = 7.1 mm), 1.1 mm clearance
# to the cable hole at R = 6. The cap's "north" pad lands directly under
# the LED's VDD pad row.
LED_RING_CAP_RADIAL_OFFSET = 3.4
# Per-LED override: a LARGER offset pulls the cap toward the ring centre
# (closer to the Ø12 cable hole); a SMALLER offset keeps it near the LED.
#
# i=1 (C21) / i=3 (C23): SMALLER offset 2.6 — D12/D14 sit closest to the
# J1 24 V terminal on the chord side; their caps must stay OUTSIDE the J1
# mating-plug no-go zone (silk rect PCB X ∈ [-8.73, +8.73]). With LED
# R=16.5 and offset 2.6, cap radius = 13.9 → cap PCB X = ±9.83, clear of
# the no-go silk + cap mask + DRC silk_clearance budget.
#
# i=0,4,5,6,7 (C20/C24/C25/C26/C27): v0.50 routing rework — LARGER offset
# so every one of these five caps lands at cap radius 7.0 mm (inner edge
# ~6.66 mm, ~0.66 mm clear of the Ø12 cable hole at R=6). Pulling them in
# toward the hole vacates the annulus just inside the LED ring, giving the
# SK6812 data-chain hops a clear lane — the autorouter could not close
# D14-DOUT / D16-DOUT in the v0.50 87/89 run. C20/C24 LED R=11 → offset
# 4.0; C25/C26/C27 LED R=13 → offset 6.0. C21/C23 stay out (J1 no-go).
LED_RING_CAP_RADIAL_OFFSET_OVERRIDE = {0: 4.0, 1: 2.6, 3: 2.6,
                                       4: 4.0, 5: 6.0, 6: 6.0, 7: 6.0}

# SK6812-SIDE package + pad geometry (body-local frame; +X = long-axis,
# +Y = short-axis pointing toward the pad-row face; emission face at -Y).
#
# Body + land pattern are taken from the LCSC/EasyEDA footprint of the
# exact ordered part C5378721 (OPSCO SK6812SIDE-A) -- the same data
# JLCPCB's DFM resolves "Pin without a pad" against -- cross-checked
# against the Normand SPC/SK6812 SIDE-A Rev.01 datasheet section 4.
#
# The package is 4.0 (L) x 1.6 (W, PCB plane) x 2.0 (H) mm. NOTE the
# datasheet marketing string "4.0x2.0x1.6mm" is L x H x W -- earlier
# boardgen revisions mis-read it as L x W x H, producing a 4.0x2.0 body
# and a SYMMETRIC 4 x 0.60 mm land. The real part terminals are
# ASYMMETRIC, so JLCPCB's part model did not land on that copper -> a
# DANGER "Pin without a pad" on the two outer pins in JLCPCB DFM.
SK6812SIDE_BODY_W = 4.0              # mm, long axis (pad row direction)
SK6812SIDE_BODY_H = 1.6             # mm, short axis (radial / emission-perp)
SK6812SIDE_BODY_Z = 2.0             # mm, height standing above PCB (<< 17 mm)
SK6812SIDE_PAD_HEIGHT = 1.2         # mm along short axis (Y) -- all 4 pads
SK6812SIDE_PAD_Y = 0.15             # mm, body-local +Y of pad-row centerline.
# This is the COPPER pad-row position, re-centred on where JLCPCB lands
# the part pins -- NOT the raw EasyEDA pad-vs-body offset (0.575 mm).
# JLCPCB places the part by its footprint ORIGIN; for C5378721 that
# origin (EasyEDA "head", y=3001.7715) sits on the pad row, ~0.56 mm off
# the body centre that our footprint anchors on. With the copper at the
# raw 0.575 mm the JLCPCB DFM "pin inner edge" check flagged every ring
# LED pin 0.2 mm past the pad inner edge. 0.15 mm re-centres the copper
# on the pins (~0.225 mm fillet all round). Emission face at body-local -Y.
# Per-pad land geometry -- (body-local center X, pad width) in mm; pad
# heights are uniform (SK6812SIDE_PAD_HEIGHT). Pad 1 = DIN (leftmost),
# 2 = VDD, 3 = DOUT, 4 = GND. Asymmetric: the outer pads are the widest,
# pad 3 (DOUT) the narrowest.
#
# Pads 2 / 3 are verbatim EasyEDA C5378721. Pads 1 / 4 (the L-shaped end
# terminals) are EasyEDA + 0.10 mm extension on the INNER edge only.
# Reason: EasyEDA's own C5378721 land draws pads 1/4 flush with the
# part's pin inner edge (pad inner edge == pin inner edge, 0 mm margin) —
# which trips JLCPCB DFM DANGER "pin right edge" / "pin left edge" (a pin
# edge level with the pad edge leaves no solder-fillet margin; only the
# 90/180/270-deg ring LEDs flag, but the condition is rotation-agnostic).
# Extending the inner edge 0.10 mm toward the body centre gives the pin a
# 0.10 mm margin (pads 2/3 already clear the check at 0.05 mm). Outer
# edges (X = +/-2.30) are unchanged, so the courtyard extent is
# unaffected; the pin-1 dot (derived from pad 1's inner edge) shifts
# 0.10 mm toward centre, away from the daughterboard silk.
SK6812SIDE_PADS: tuple[tuple[float, float], ...] = (
    (-1.750, 1.10),   # pad 1 = DIN  (EasyEDA 1.00 + 0.10 mm inner margin)
    (-0.450, 0.70),   # pad 2 = VDD
    (+0.575, 0.45),   # pad 3 = DOUT
    (+1.750, 1.10),   # pad 4 = GND  (EasyEDA 1.00 + 0.10 mm inner margin)
)
# Derived: body-local center X of each pad (pin-1 dot, silk labels).
SK6812SIDE_PAD_X_OFFSETS = tuple(x for x, _w in SK6812SIDE_PADS)

# Littelfuse 1812L-series PTC fuse — land pattern + body geometry.
#
# F1 (the 24 V input PTC) is the Littelfuse 1812L075/33DR (LCSC C151170,
# 33 V / 750 mA hold / 1.5 A trip). KiCad stock `Fuse:Fuse_1812_4532Metric`
# is a GENERIC IPC-7351 1812 chip-fuse land (pad pitch 4.275 mm, gap
# 3.15 mm) — it does NOT match this part's terminal geometry. The
# Littelfuse 1812L termination bands are wide, so the recommended land is
# tighter: pad pitch 3.707 mm, gap 2.30 mm. On the generic stock land the
# part's pin inner edge sat 0.43 mm past the copper -> JLCPCB DFM DANGER
# "pin inner edge". The numbers below are the verbatim EasyEDA F1812
# footprint of C151170 (1 EasyEDA unit = 0.254 mm) — the exact data
# JLCPCB's DFM resolves against. Consumed by oas:Fuse_1812L_4532Metric.
#
# (An earlier revision carried LCSC C262023 here, believed to be the
# Littelfuse part — it is actually TLC-MSMD050, a 15 V / 500 mA fuse,
# under-rated for the 24 V rail. Caught by the EasyEDA cross-check before
# any order was placed, per CLAUDE.md Lesson 5.)
FUSE1812L_BODY_W = 4.55      # mm, body long axis  (X) — EasyEDA gge999 span
FUSE1812L_BODY_H = 3.24      # mm, body short axis (Y) — EasyEDA gge999 span
FUSE1812L_BODY_Z = 1.10     # mm, max height above PCB (Littelfuse 1812L)
FUSE1812L_PAD_W = 1.4067    # mm, pad width  (X) — EasyEDA 5.5381 u
FUSE1812L_PAD_H = 3.4992    # mm, pad height (Y) — EasyEDA 13.7764 u
FUSE1812L_PAD_X = 1.8534    # mm, |body-local centre X| of each pad — 7.297 u


def _led_ring_position(index: int) -> tuple[float, float, float]:
    """Return (PCB_x, PCB_y, kicad_rotation_deg) for the i-th LED on the ring.

    i = 0 → D11 at θ = 0° (PCB +X axis), i = 1 → D12 at θ = 30°, etc.
    The rotation is set so the LED's emission face (body-local -Y) points
    radially OUTWARD from the PCB origin.
    """
    theta_deg = LED_RING_THETA_START_DEG + index * LED_RING_THETA_STEP_DEG
    theta_rad = math.radians(theta_deg)
    r = LED_RING_RADIUS_OVERRIDE.get(index, LED_RING_RADIUS)
    px = r * math.cos(theta_rad)
    py = r * math.sin(theta_rad)
    # KiCad rotation = (90 - θ) mod 360. KiCad uses CCW rotation for
    # positive angles. At θ=0 (D11 on +X axis), rot=90 maps body-local
    # emission (0, -1) CCW to PCB (+1, 0) = OUTWARD. At θ=180 (D15 on
    # -X axis), rot=270 maps (0, -1) CCW to (-1, 0) = OUTWARD. (v0.41
    # 2026-05-19: previous formula was (270 - θ) which produced INWARD
    # emission — verified visually on 3D render after SK6812-SIDE-A.step
    # was added.) Because (90 - θ) already differs from the old
    # (270 - θ) by 180°, the placement formula itself now carries the
    # JLCPCB tape-feeder compensation: the SK6812-SIDE entry in
    # JLCPCB_ROTATIONS_OAS (pipeline/jlcpcb/_rotations.py) is therefore
    # 0°. Adding a +180° there on top of (90 - θ) double-compensates
    # and lands every LED 180° off on JLCPCB DFM (emission inward,
    # pin-outer-edge danger). Keep that entry at 0°.
    # body-local emission face is at -Y; to point that face RADIALLY OUTWARD
    # from the ring center for an LED placed at angle theta_deg, we need
    # rotation = 90deg - theta_deg (mod 360). Earlier formula used
    # (270 - theta_deg) which pointed emission INWARD (180deg flipped).
    rot = int(round((90.0 - theta_deg) % 360.0))
    return (px, py, rot)


def _led_cap_position(index: int) -> tuple[float, float, float]:
    """Return (PCB_x, PCB_y, kicad_rotation_deg) for the i-th LED's
    decoupling cap (C20 + index).

    The cap sits radially INWARD from the LED, at radius
    LED_RING_RADIUS - LED_RING_CAP_RADIAL_OFFSET. The cap's KiCad
    rotation matches the LED's rotation so the cap body lies tangentially
    (consistent visual orientation around the ring).
    """
    theta_deg = LED_RING_THETA_START_DEG + index * LED_RING_THETA_STEP_DEG
    theta_rad = math.radians(theta_deg)
    led_r = LED_RING_RADIUS_OVERRIDE.get(index, LED_RING_RADIUS)
    cap_offset = LED_RING_CAP_RADIAL_OFFSET_OVERRIDE.get(
        index, LED_RING_CAP_RADIAL_OFFSET)
    cap_r = led_r - cap_offset
    px = cap_r * math.cos(theta_rad)
    py = cap_r * math.sin(theta_rad)
    # body-local emission face is at -Y; to point that face RADIALLY OUTWARD
    # from the ring center for an LED placed at angle theta_deg, we need
    # rotation = 90deg - theta_deg (mod 360). Earlier formula used
    # (270 - theta_deg) which pointed emission INWARD (180deg flipped).
    rot = int(round((90.0 - theta_deg) % 360.0))
    return (px, py, rot)
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
